nopcall/hitboard/HitboardAir/01_刷机/Pico正面.png

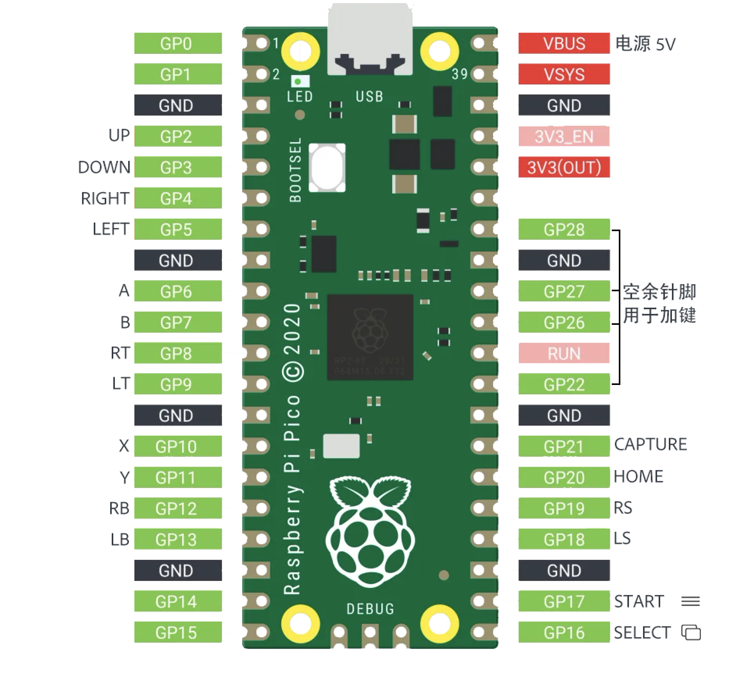
HitboardAir/01_刷机/Pico正面.png
