nopcall/hitboard/HitboardAir/02_3D_Files/images/00_按键.png

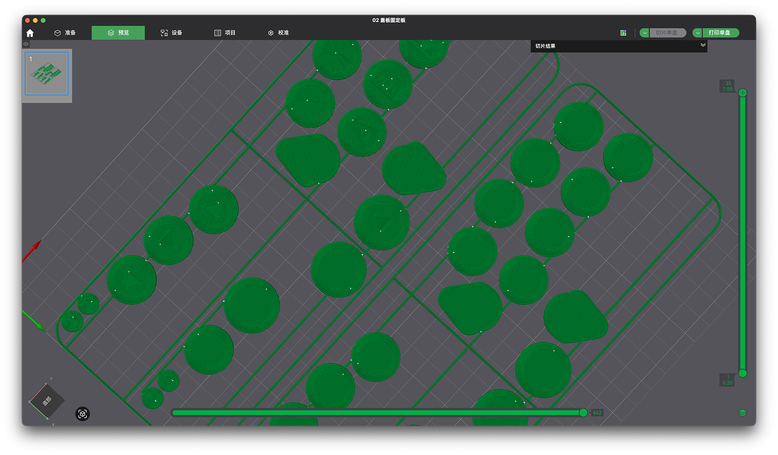
HitboardAir/02_3D_Files/images/00_按键.png
