nopcall/hitboard/HitboardAir/02_3D_Files/images/产品实拍_PLA.jpg

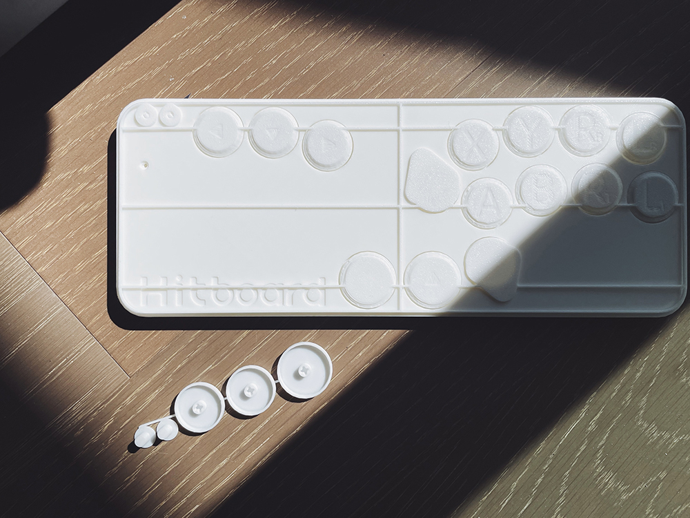
HitboardAir/02_3D_Files/images/产品实拍_PLA.jpg
