nopcall/hitboard/HitboardAir/02_3D_Files/More - 更多配件 /00_按键配件/配件_标准按键/00_圆润按键 （单个）/圆润按键.png

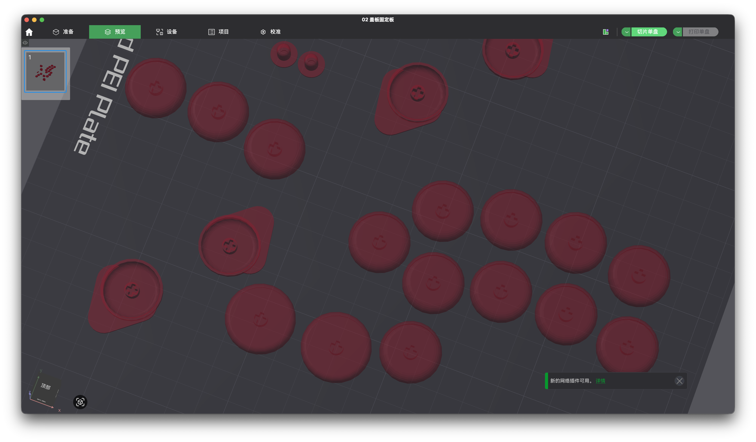
HitboardAir/02_3D_Files/More - 更多配件 /00_按键配件/配件_标准按键/00_圆润按键 （单个）/圆润按键.png
