nopcall/hitboard/HitboardAir/03_亚克力CAD文件/对称版/对称版布局示意图.png

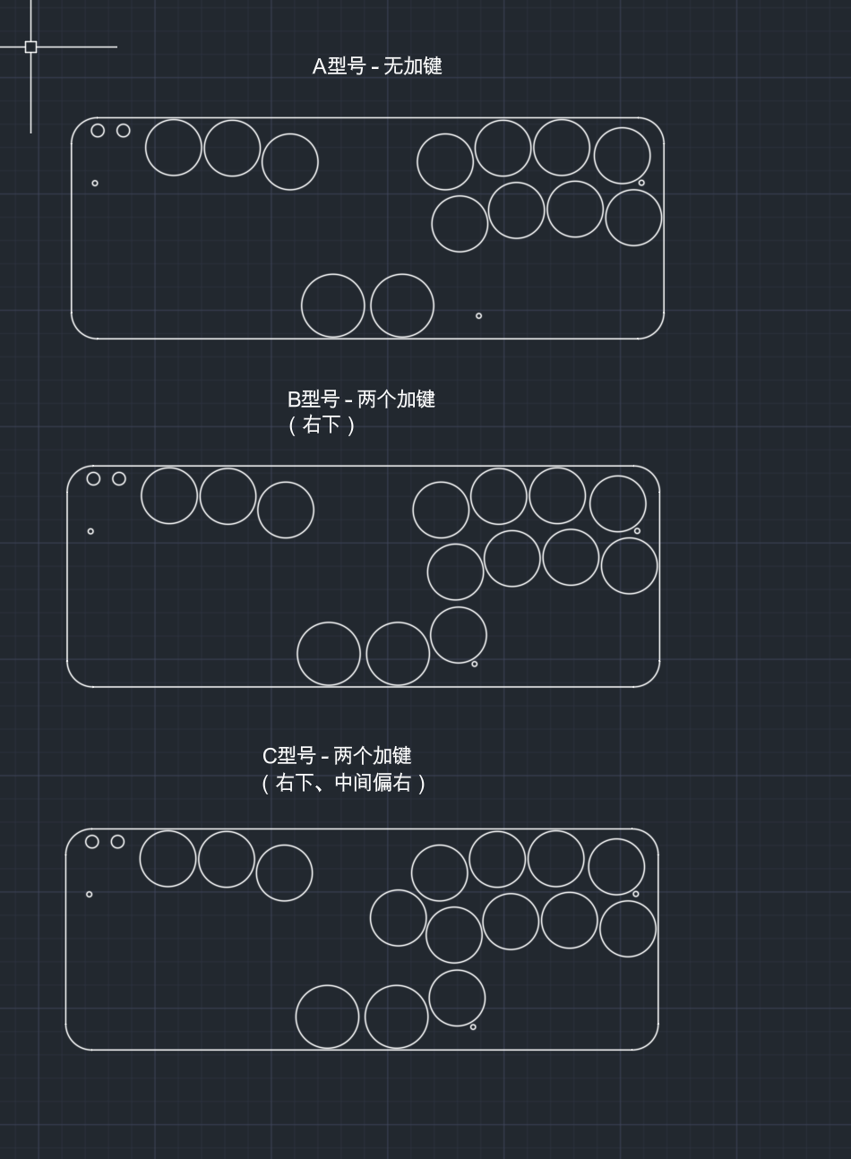
HitboardAir/03_亚克力CAD文件/对称版/对称版布局示意图.png
