nopcall/hitboard/HitboardAir/images/Dock.JPG

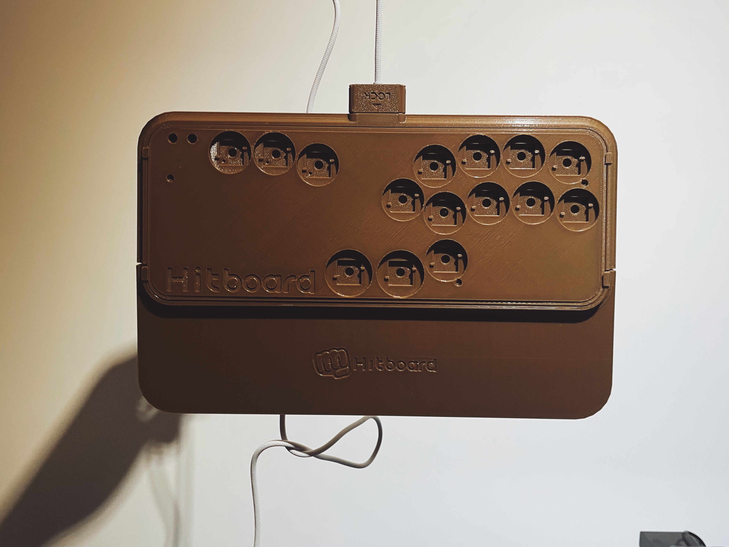
HitboardAir/images/Dock.JPG
