nopcall/hitboard/HitboardAir/images/FindYourFight03.png

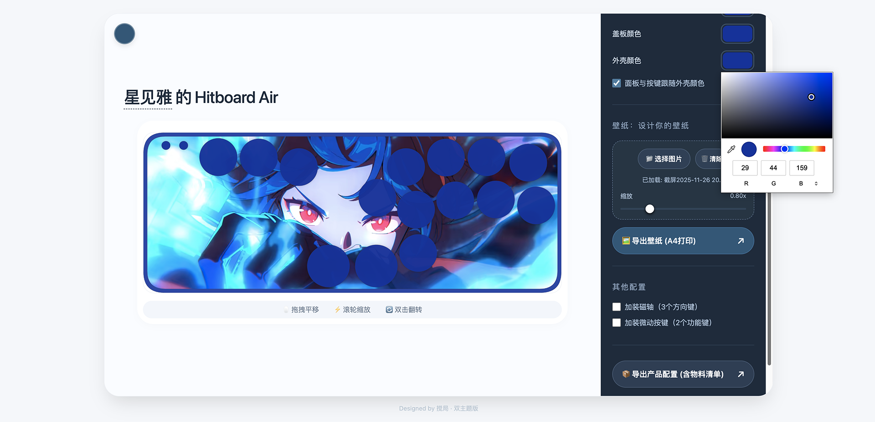
HitboardAir/images/FindYourFight03.png
