nopcall/hitboard/HitboardAir/images/FindYourFight04.png

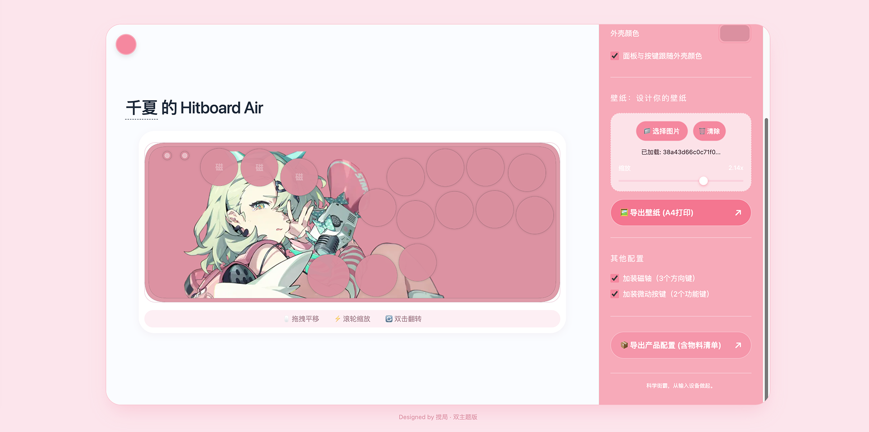
HitboardAir/images/FindYourFight04.png
