nopcall/hitboard/HitboardAir/images/边缘对比.JPG

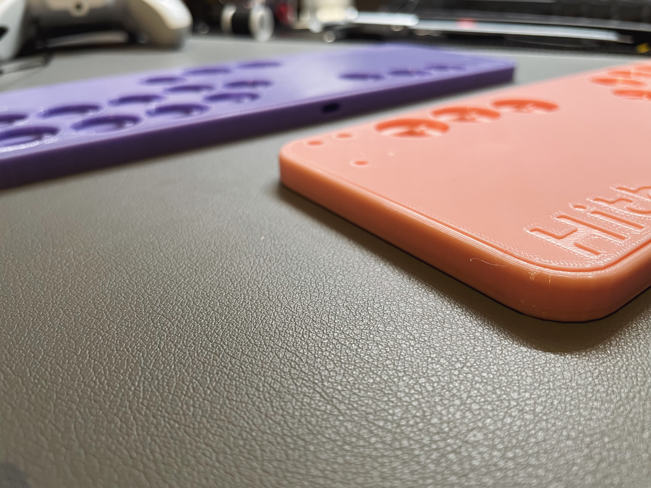
HitboardAir/images/边缘对比.JPG
