nopcall/hitboard/HitboardAir/其他/PCB 电路板/功能键电路板/PCB 小板.png

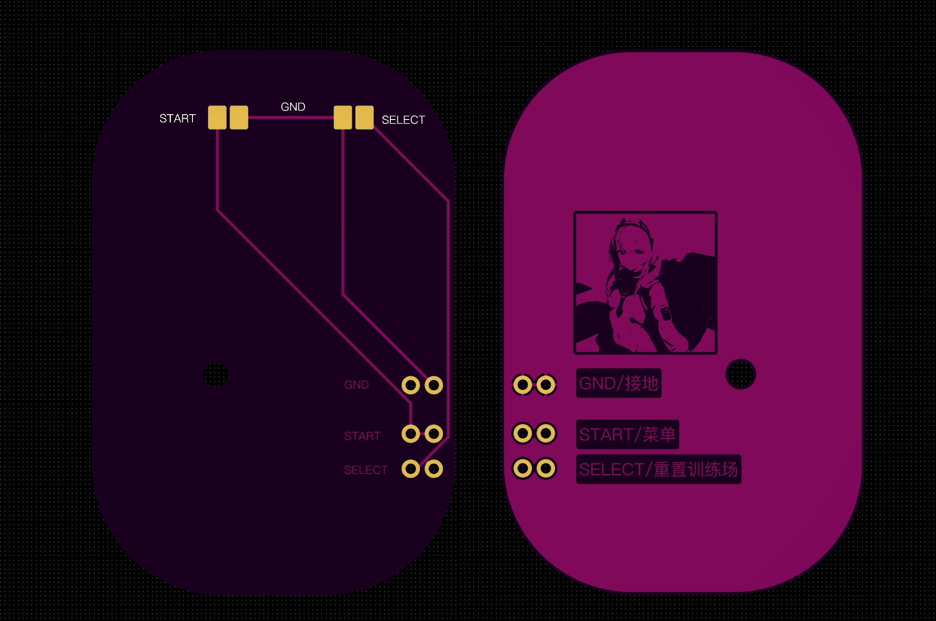
HitboardAir/其他/PCB 电路板/功能键电路板/PCB 小板.png
