nopcall/hitboard/HitboardClassic/02_3D_Files/Hitboard Classic/1-选择盖板/风格_街机:Hitbox/说明：盖板上下藏了 4 颗隐藏螺丝，如果有进一步固定需求，拿刀划开就行了.png

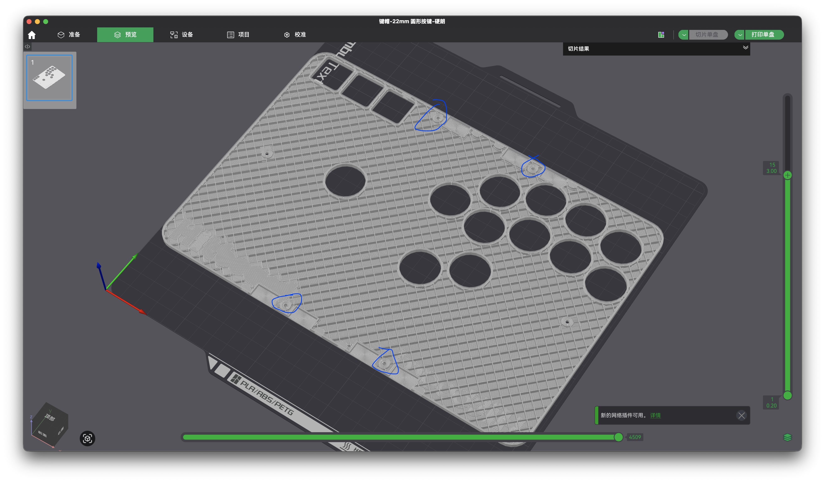
HitboardClassic/02_3D_Files/Hitboard Classic/1-选择盖板/风格_街机:Hitbox/说明：盖板上下藏了 4 颗隐藏螺丝，如果有进一步固定需求，拿刀划开就行了.png
