nopcall/hitboard/HitboardZero/元器件规格书/led 规格.png

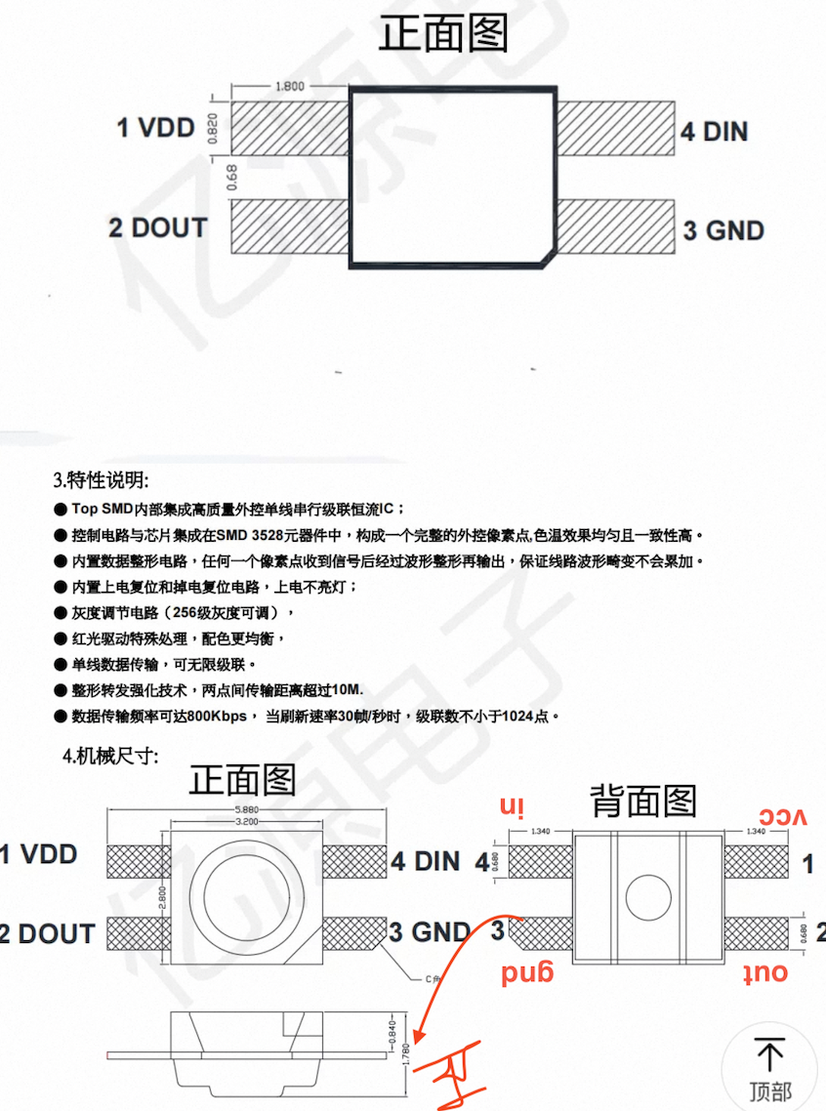
HitboardZero/元器件规格书/led 规格.png
