nopcall/hitboard/HitboardZero/元器件规格书/轴座规格.JPG

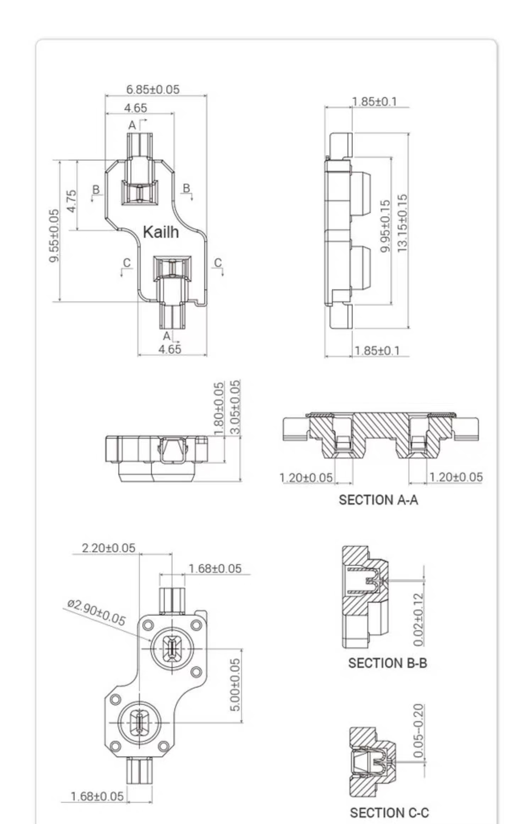
HitboardZero/元器件规格书/轴座规格.JPG
