nopcall/hitboard/HitboardClassic/02_3D_Files/Hitboard Classic - 大杯 L/新大杯 （L）/外壳-左半.stl

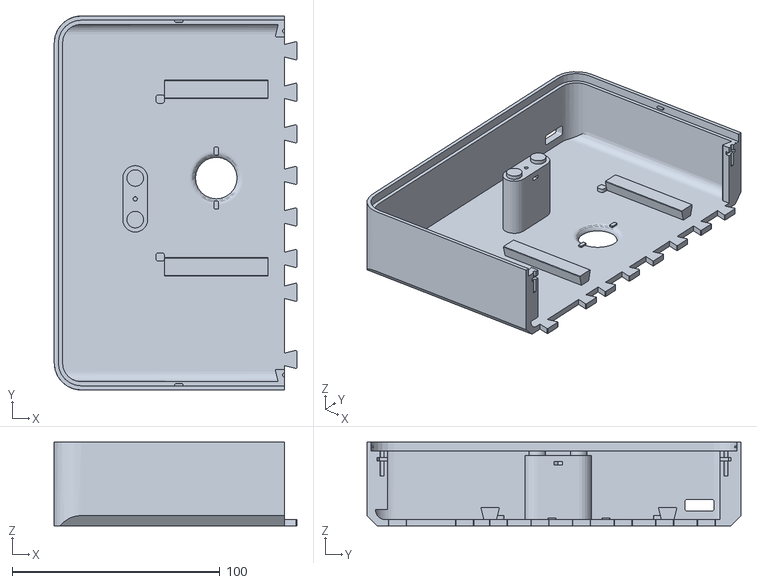
[picture p57: CAD file, 2026-05-05]
HitboardClassic/02_3D_Files/Hitboard Classic - 大杯 L/新大杯 （L）/外壳-左半.stl
116.7 x 180.0 x 40.4
