nopcall/hitboard/HitboardClassic/02_3D_Files/Hitboard Classic - 大杯 L/新大杯 （L）/更多（有完整外壳）/外壳-290x180.stl

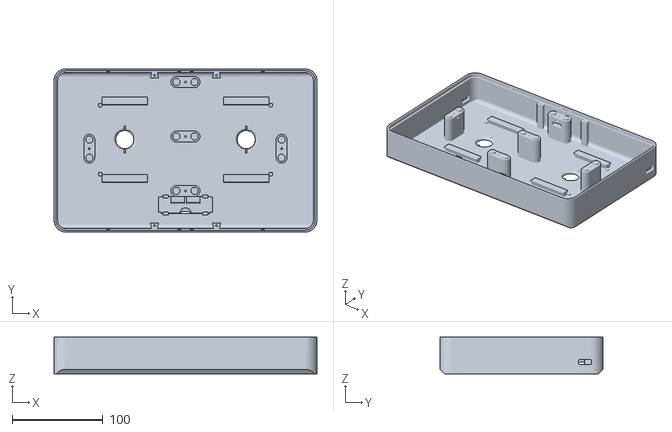
[picture p58: CAD file, 2026-05-06]
HitboardClassic/02_3D_Files/Hitboard Classic - 大杯 L/新大杯 （L）/更多（有完整外壳）/外壳-290x180.stl
290.0 x 180.0 x 40.4
