nopcall/hitboard/HitboardClassic/02_3D_Files/Hitboard Classic/1-选择盖板/风格_Mixbox/盖板-Mixbox（混合）.stl

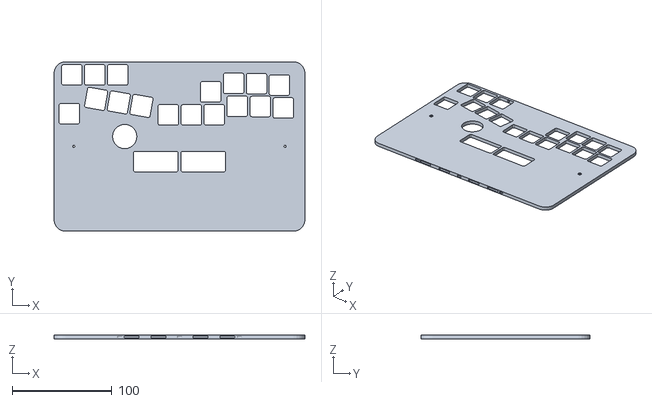
[picture p60: CAD file, 2026-05-03]
HitboardClassic/02_3D_Files/Hitboard Classic/1-选择盖板/风格_Mixbox/盖板-Mixbox（混合）.stl
252.0 x 170.0 x 4.00
