nopcall/hitboard/HitboardClassic/02_3D_Files/Hitboard Classic/1-选择盖板/风格_街机:Hitbox/盖板-街机（纯血）.stl

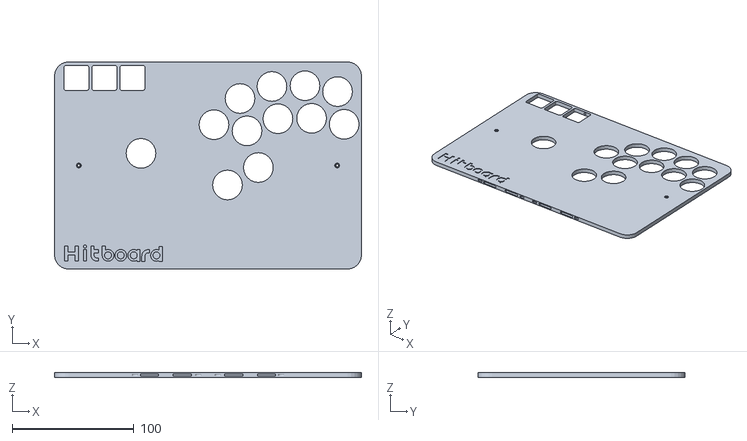
[picture p61: CAD file, 2026-05-04]
HitboardClassic/02_3D_Files/Hitboard Classic/1-选择盖板/风格_街机:Hitbox/盖板-街机（纯血）.stl
252.0 x 170.0 x 4.00
