nopcall/hitboard/HitboardClassic/02_3D_Files/Hitboard Classic/2-选择按键/街机:Hitbox/选项 B-凯华矮轴按键方案/键帽-22mm 圆形按键-圆润.stl

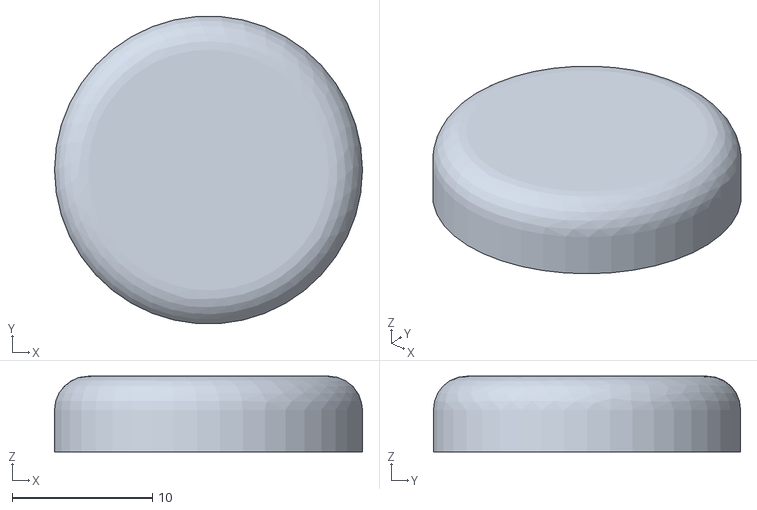
[picture p62: CAD file, 2026-05-10]
HitboardClassic/02_3D_Files/Hitboard Classic/2-选择按键/街机:Hitbox/选项 B-凯华矮轴按键方案/键帽-22mm 圆形按键-圆润.stl
22.0 x 21.9 x 5.40
