nopcall/hitboard/HitboardClassic/02_3D_Files/Hitboard Classic/3-选择外壳/外壳本体.stl

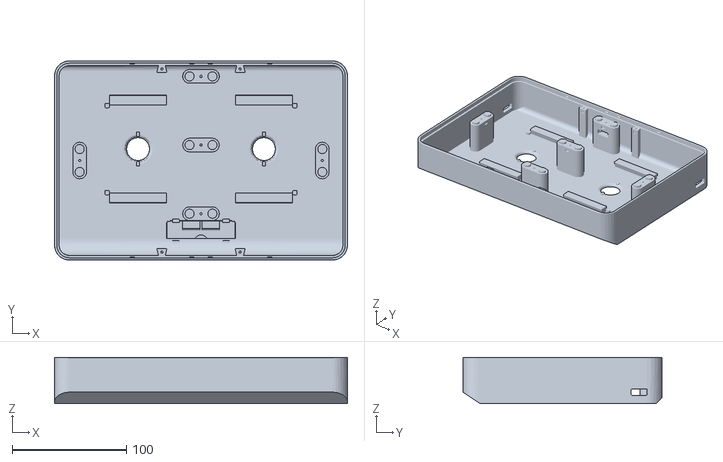
[picture p64: CAD file, 2026-05-05]
HitboardClassic/02_3D_Files/Hitboard Classic/3-选择外壳/外壳本体.stl
256.0 x 174.0 x 40.4
