nopcall/hitboard/HitboardClassic/02_3D_Files/Hitboard Classic/4-摇杆配件/摇杆色彩环.stl

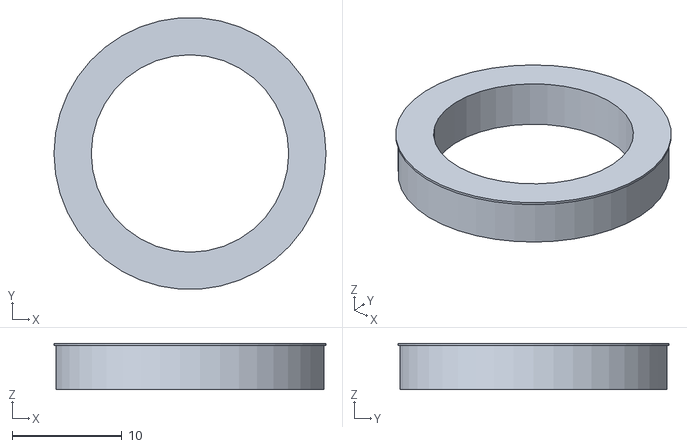
[picture p65: CAD file, 2026-04-30]
HitboardClassic/02_3D_Files/Hitboard Classic/4-摇杆配件/摇杆色彩环.stl
24.8 x 24.7 x 4.20
