nopcall/hitboard/HitboardClassic/02_3D_Files/More - 更多配件 /00_按键/01_轴座/轴座-Mixboard 宽按键-MX轴(打印时开启支撑).stl

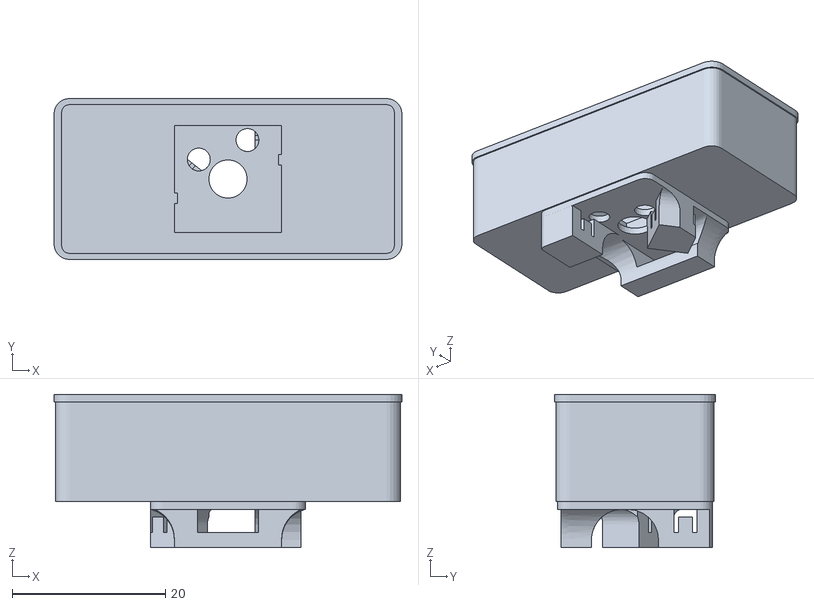
[picture p66: CAD file, 2026-05-03]
HitboardClassic/02_3D_Files/More - 更多配件 /00_按键/01_轴座/轴座-Mixboard 宽按键-MX轴(打印时开启支撑).stl
45.4 x 21.0 x 20.0
