nopcall/hitboard/HitboardClassic/02_3D_Files/More - 更多配件 /00_按键/02_矮轴按键/轴座-圆形按键-矮轴.stl

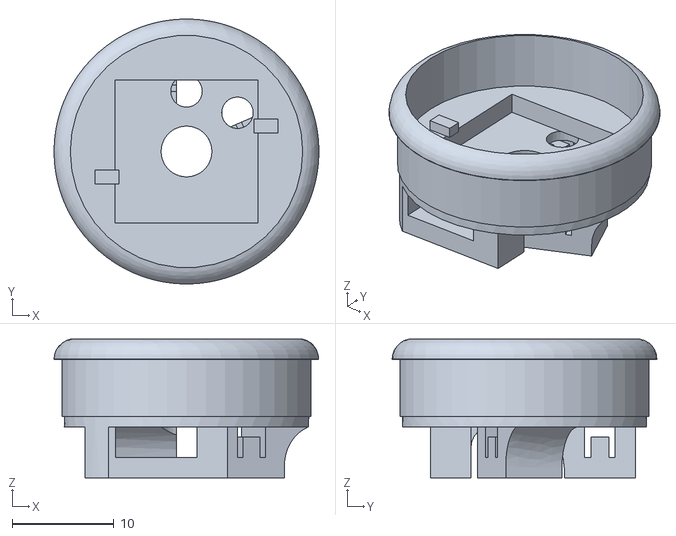
[picture p67: CAD file, 2026-04-30]
HitboardClassic/02_3D_Files/More - 更多配件 /00_按键/02_矮轴按键/轴座-圆形按键-矮轴.stl
26.0 x 26.0 x 13.6
