nopcall/hitboard/HitboardClassic/02_3D_Files/More - 更多配件 /01_盖板配件/封帽圆.stl

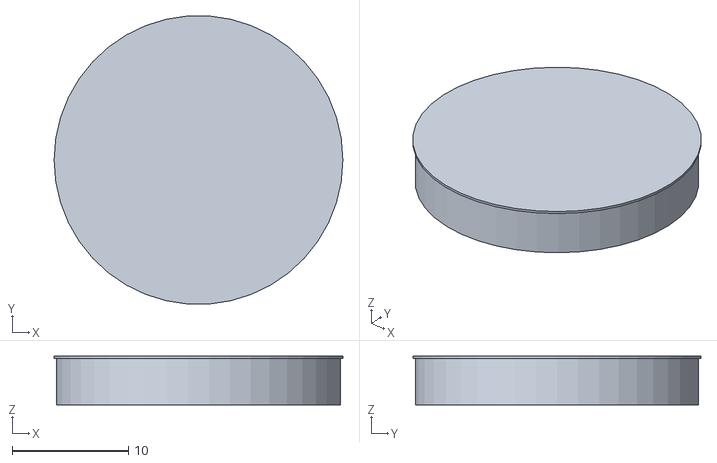
[picture p69: CAD file, 2026-04-30]
HitboardClassic/02_3D_Files/More - 更多配件 /01_盖板配件/封帽圆.stl
24.8 x 24.7 x 4.20
