nopcall/hitboard/HitboardClassic/02_3D_Files/More - 更多配件 /02_外壳配件/封帽-typec接口.stl

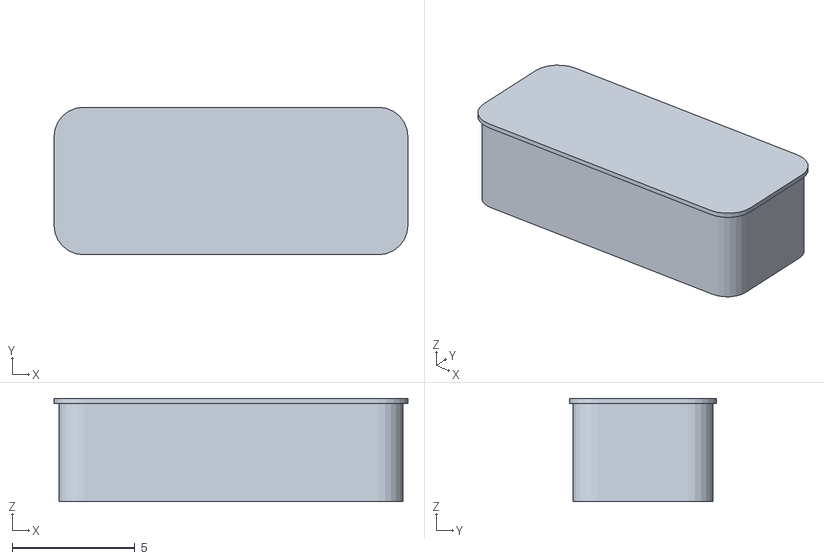
[picture p70: CAD file, 2026-05-03]
HitboardClassic/02_3D_Files/More - 更多配件 /02_外壳配件/封帽-typec接口.stl
14.4 x 6.00 x 4.20
