nopcall/hitboard/HitboardClassic/02_3D_Files/More - 更多配件 /03_其他配件/壁纸支撑板/支撑板-标准版-Mixbox.stl

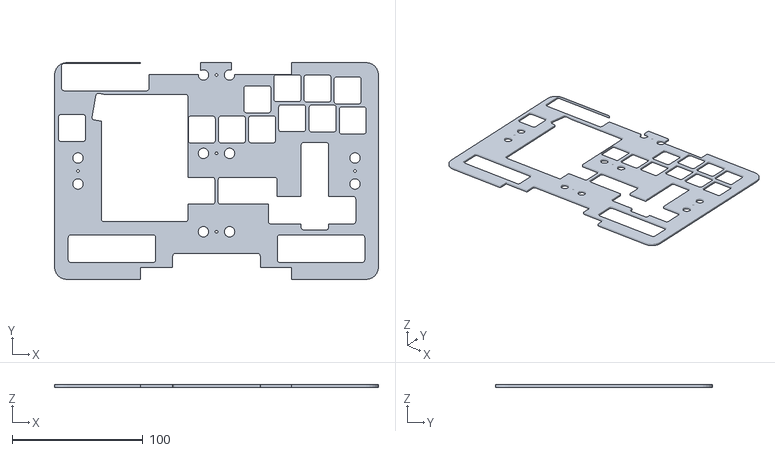
[picture p71: CAD file, 2026-04-28]
HitboardClassic/02_3D_Files/More - 更多配件 /03_其他配件/壁纸支撑板/支撑板-标准版-Mixbox.stl
248.0 x 166.0 x 2.00
