nopcall/hitboard/HitboardClassic/02_3D_Files/More - 更多配件 /03_其他配件/电源套件/电池仓 2 节 5 号.stl

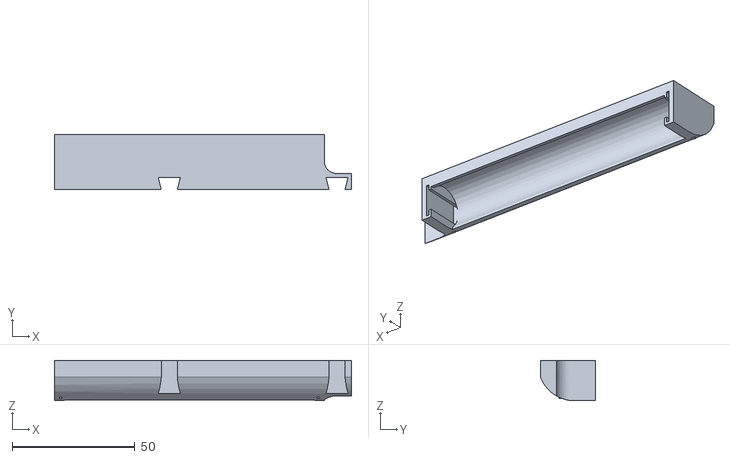
[picture p72: CAD file, 2026-05-03]
HitboardClassic/02_3D_Files/More - 更多配件 /03_其他配件/电源套件/电池仓 2 节 5 号.stl
121.1 x 22.6 x 16.5
