nopcall/hitboard/HitboardClassic/02_3D_Files/More - 更多配件 /03_其他配件/试轴器-圆 x3.stl

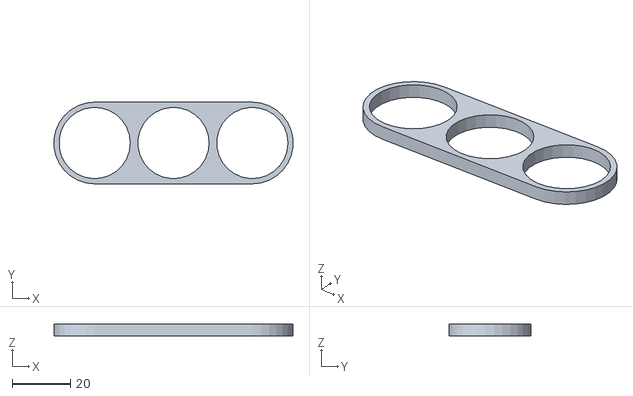
[picture p73: CAD file, 2026-04-30]
HitboardClassic/02_3D_Files/More - 更多配件 /03_其他配件/试轴器-圆 x3.stl
81.8 x 28.0 x 4.00
