nopcall/hitboard/HitboardAir/02_3D_Files/180x180 打印机（A1mini ）/七星版（可加 w、shift 键）/圆润/04_外壳_圆润_右半.stl

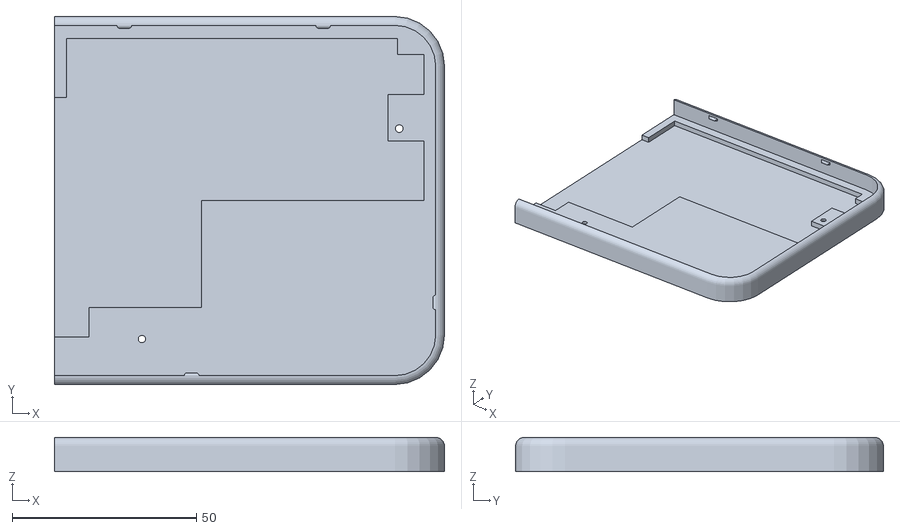
[picture p74: CAD file, 2026-04-25]
HitboardAir/02_3D_Files/180x180 打印机（A1mini ）/七星版（可加 w、shift 键）/圆润/04_外壳_圆润_右半.stl
106.0 x 100.0 x 9.30
