nopcall/hitboard/HitboardAir/02_3D_Files/180x180 打印机（A1mini ）/对称版/圆润/04_外壳_圆润_左半.stl

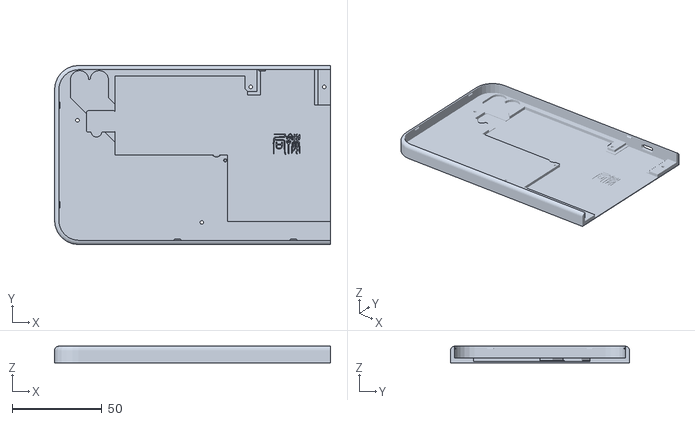
[picture p76: CAD file, 2026-04-25]
HitboardAir/02_3D_Files/180x180 打印机（A1mini ）/对称版/圆润/04_外壳_圆润_左半.stl
154.0 x 100.0 x 9.30
