nopcall/hitboard/HitboardAir/02_3D_Files/Hitboard Air - 七星版（拳皇:绝区零:音游）/圆润线条/03 线路板.stl

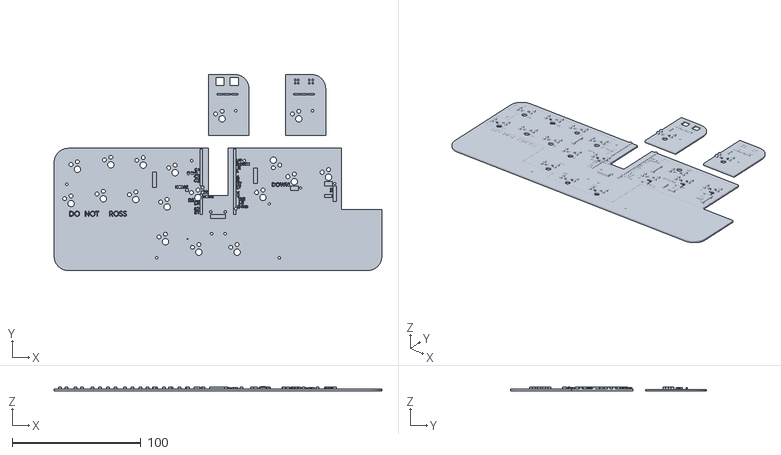
[picture p77: CAD file, 2026-04-25]
HitboardAir/02_3D_Files/Hitboard Air - 七星版（拳皇:绝区零:音游）/圆润线条/03 线路板.stl
255.2 x 152.6 x 3.50
