nopcall/hitboard/HitboardAir/02_3D_Files/More - 更多配件 /00_按键配件/配件_加键/圆形（22mm 直径）.stl

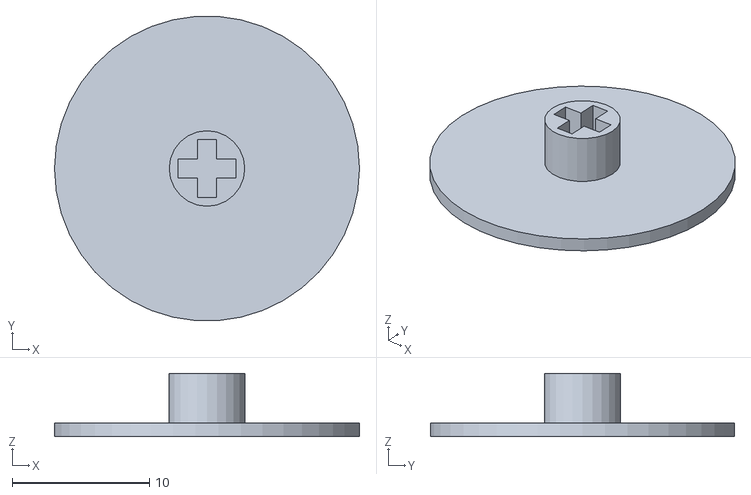
[picture p80: CAD file, 2026-04-25]
HitboardAir/02_3D_Files/More - 更多配件 /00_按键配件/配件_加键/圆形（22mm 直径）.stl
22.2 x 22.1 x 4.60
