nopcall/hitboard/HitboardAir/02_3D_Files/More - 更多配件 /02_盖板配件/23mm 按键封帽_改方孔.stl

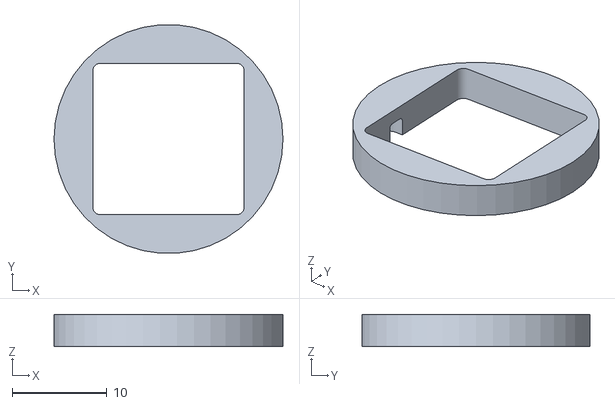
[picture p81: CAD file, 2026-04-25]
HitboardAir/02_3D_Files/More - 更多配件 /02_盖板配件/23mm 按键封帽_改方孔.stl
24.2 x 24.1 x 3.40
