nopcall/hitboard/HitboardAir/02_3D_Files/More - 更多配件 /03_线路板配件/03_小板_缠线适配导电胶.stl

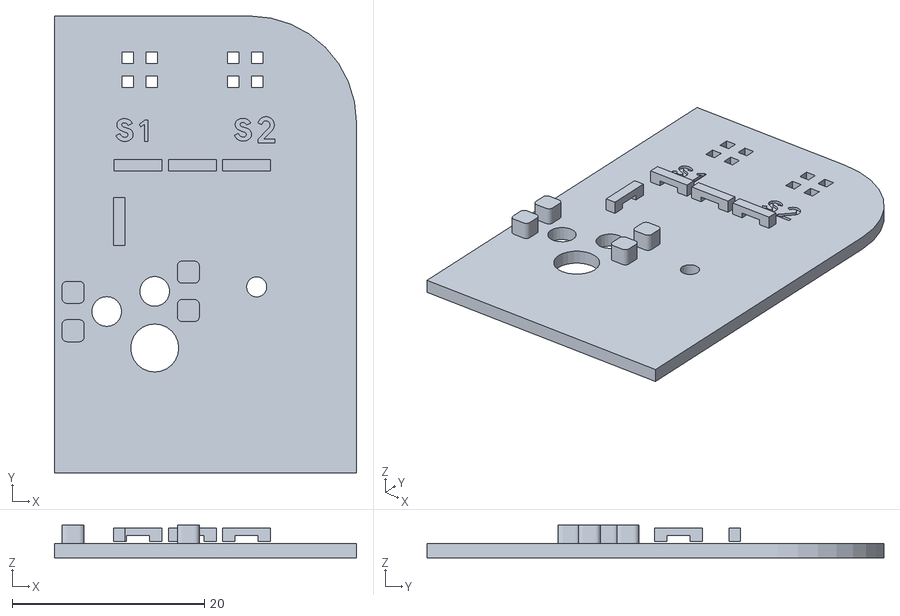
[picture p82: CAD file, 2026-04-25]
HitboardAir/02_3D_Files/More - 更多配件 /03_线路板配件/03_小板_缠线适配导电胶.stl
31.5 x 47.6 x 3.40
