nopcall/hitboard/HitboardClassic/02_3D_Files/Hitboard Classic - 大杯 L/新大杯 （L）/外壳-右半.stl

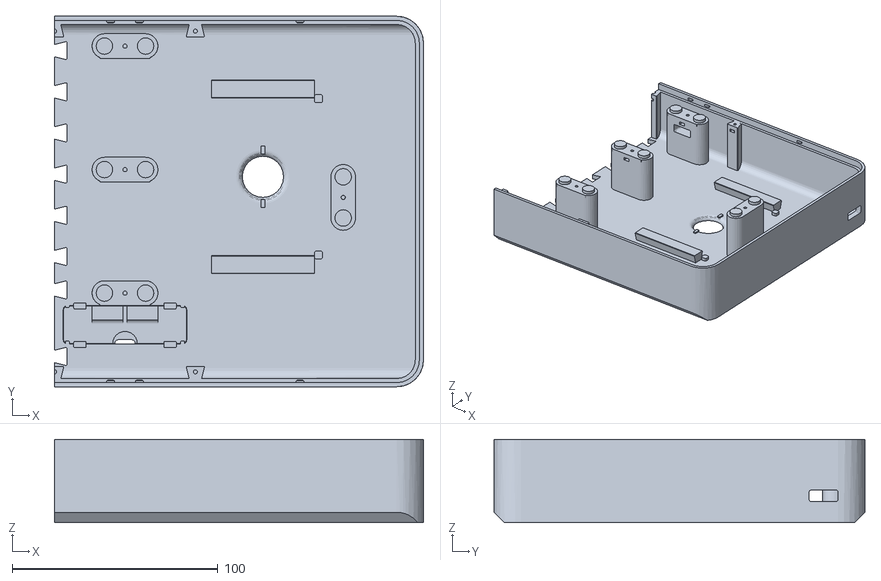
[picture p84: CAD file, 2026-05-05]
HitboardClassic/02_3D_Files/Hitboard Classic - 大杯 L/新大杯 （L）/外壳-右半.stl
179.2 x 180.0 x 40.4
