nopcall/hitboard/HitboardClassic/02_3D_Files/Hitboard Classic - 大杯 L/新大杯 （L）/更多（有完整外壳）/盖板-左半（带 Hitbox 方向键开孔）.stl

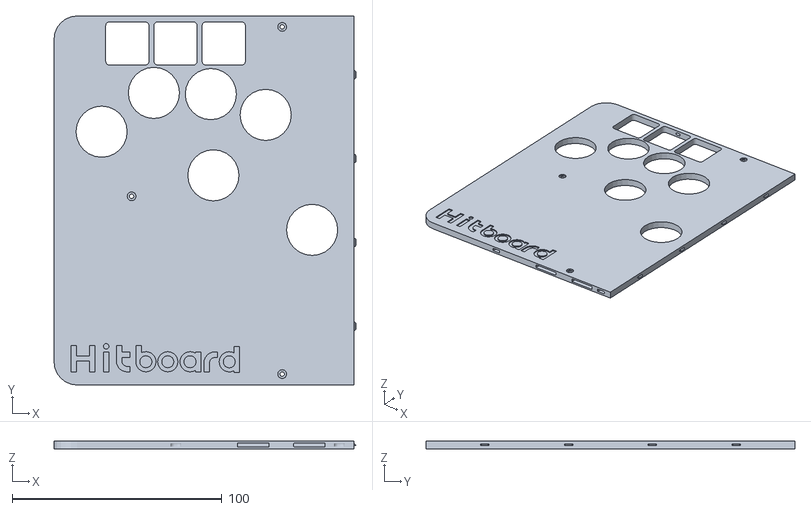
[picture p85: CAD file, 2026-05-04]
HitboardClassic/02_3D_Files/Hitboard Classic - 大杯 L/新大杯 （L）/更多（有完整外壳）/盖板-左半（带 Hitbox 方向键开孔）.stl
144.0 x 176.0 x 4.00
