nopcall/hitboard/HitboardClassic/02_3D_Files/Hitboard Classic/1-选择盖板/风格_Mixbox/180x180 打印机（A1mini ）/盖板-Mixbox（纯血）左.stl

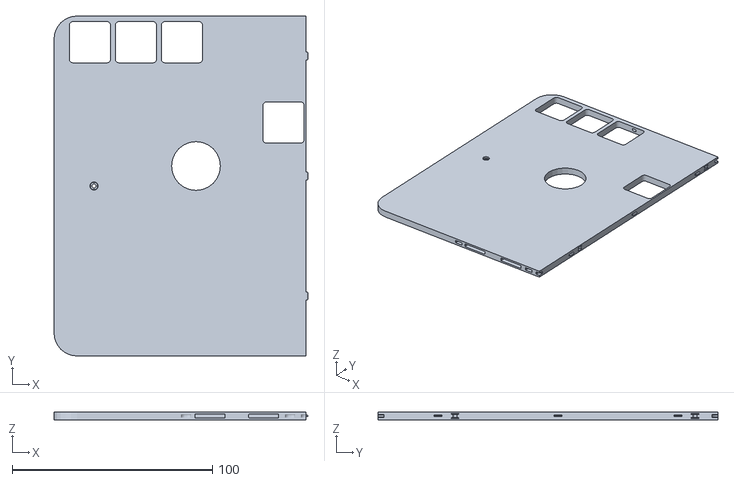
[picture p86: CAD file, 2026-05-03]
HitboardClassic/02_3D_Files/Hitboard Classic/1-选择盖板/风格_Mixbox/180x180 打印机（A1mini ）/盖板-Mixbox（纯血）左.stl
127.0 x 170.0 x 4.00
