nopcall/hitboard/HitboardClassic/02_3D_Files/Hitboard Classic/1-选择盖板/风格_街机:Hitbox/180x180 打印机（A1mini ）/盖板-街机（纯血）左.stl

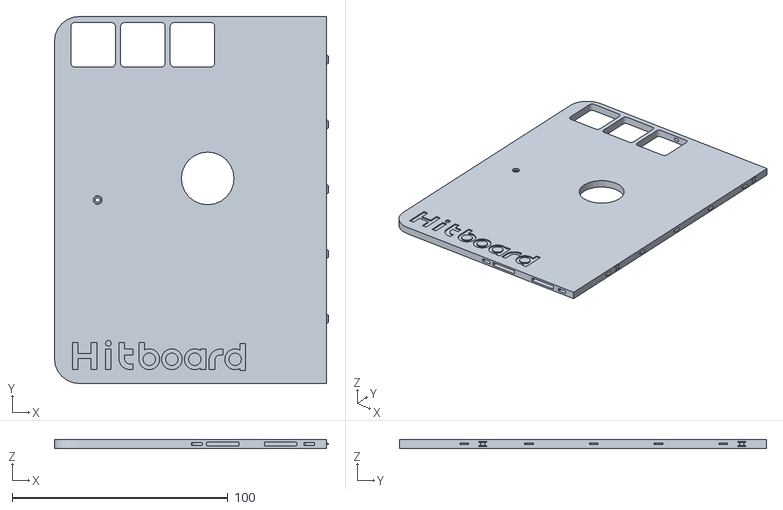
[picture p87: CAD file, 2026-05-04]
HitboardClassic/02_3D_Files/Hitboard Classic/1-选择盖板/风格_街机:Hitbox/180x180 打印机（A1mini ）/盖板-街机（纯血）左.stl
127.0 x 170.0 x 4.00
