nopcall/hitboard/HitboardClassic/02_3D_Files/Hitboard Classic/3-选择外壳/180x180 打印机（A1mini ）/外壳左半.stl

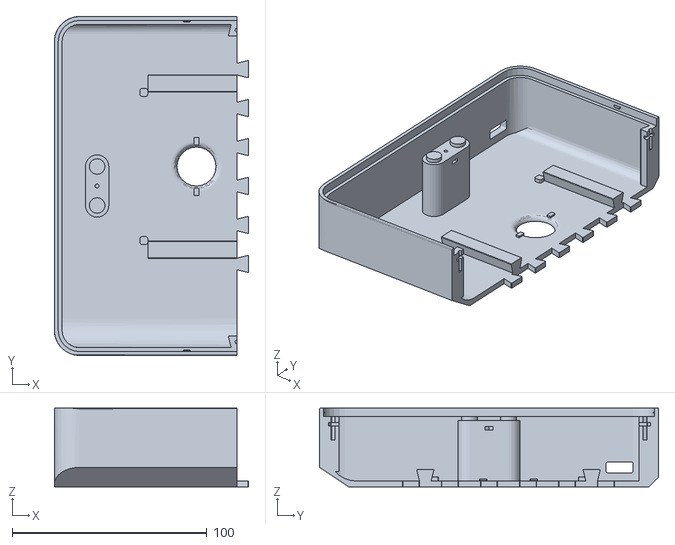
[picture p88: CAD file, 2026-05-05]
HitboardClassic/02_3D_Files/Hitboard Classic/3-选择外壳/180x180 打印机（A1mini ）/外壳左半.stl
99.8 x 174.0 x 40.4
