nopcall/hitboard/HitboardClassic/02_3D_Files/Hitboard Classic/3-选择外壳/外壳组件.stl

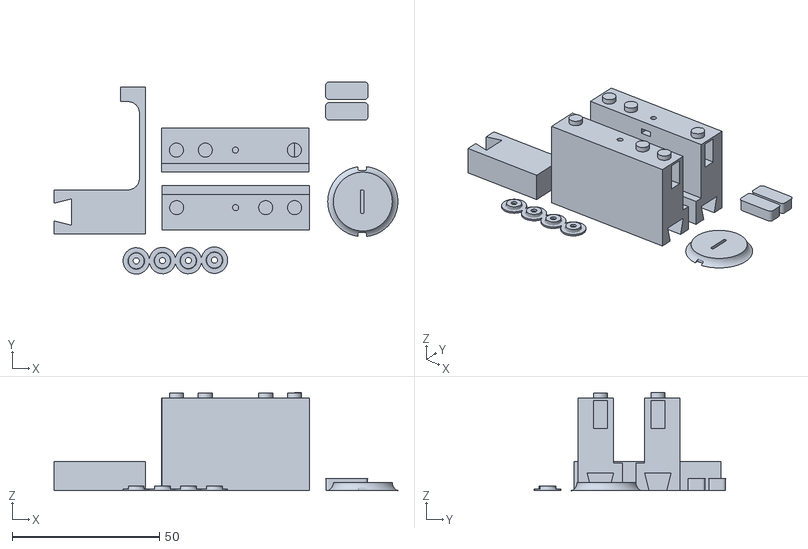
[picture p89: CAD file, 2026-05-04]
HitboardClassic/02_3D_Files/Hitboard Classic/3-选择外壳/外壳组件.stl
116.7 x 65.2 x 33.4
