nopcall/hitboard/HitboardClassic/02_3D_Files/Hitboard Classic/4-摇杆配件/摇杆防尘片.stl

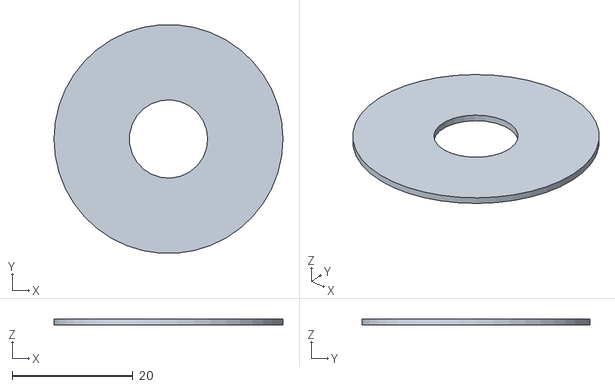
[picture p90: CAD file, 2026-04-22]
HitboardClassic/02_3D_Files/Hitboard Classic/4-摇杆配件/摇杆防尘片.stl
38.0 x 37.9 x 1
