nopcall/hitboard/HitboardClassic/02_3D_Files/More - 更多配件 /00_按键/01_轴座/轴座-功能键-矮轴.stl

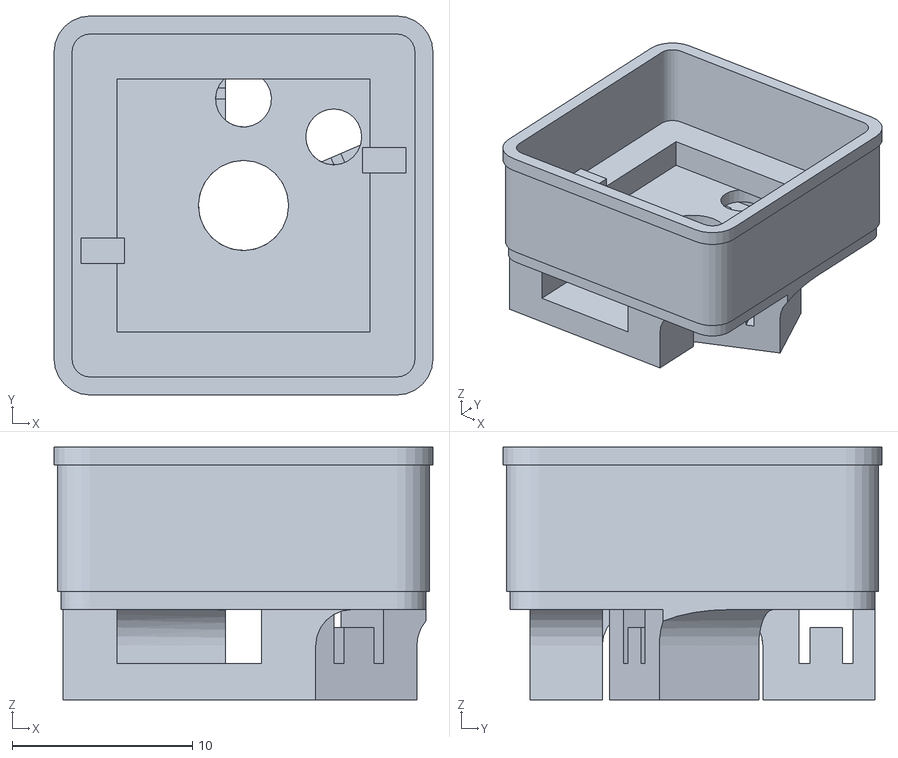
[picture p92: CAD file, 2026-05-03]
HitboardClassic/02_3D_Files/More - 更多配件 /00_按键/01_轴座/轴座-功能键-矮轴.stl
21.0 x 21.0 x 14.0
