nopcall/hitboard/HitboardClassic/02_3D_Files/More - 更多配件 /01_盖板配件/封帽-Shift.stl

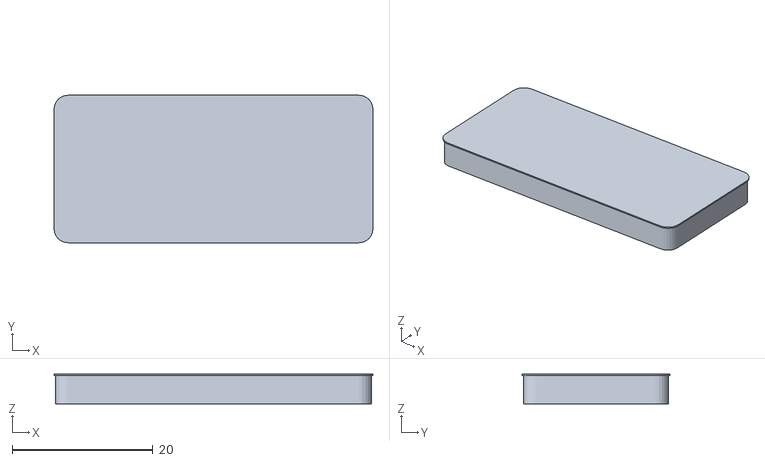
[picture p93: CAD file, 2026-04-27]
HitboardClassic/02_3D_Files/More - 更多配件 /01_盖板配件/封帽-Shift.stl
45.4 x 21.0 x 4.20
