nopcall/hitboard/HitboardClassic/02_3D_Files/More - 更多配件 /02_外壳配件/轨道-摇杆台（宝联:拳霸）.stl

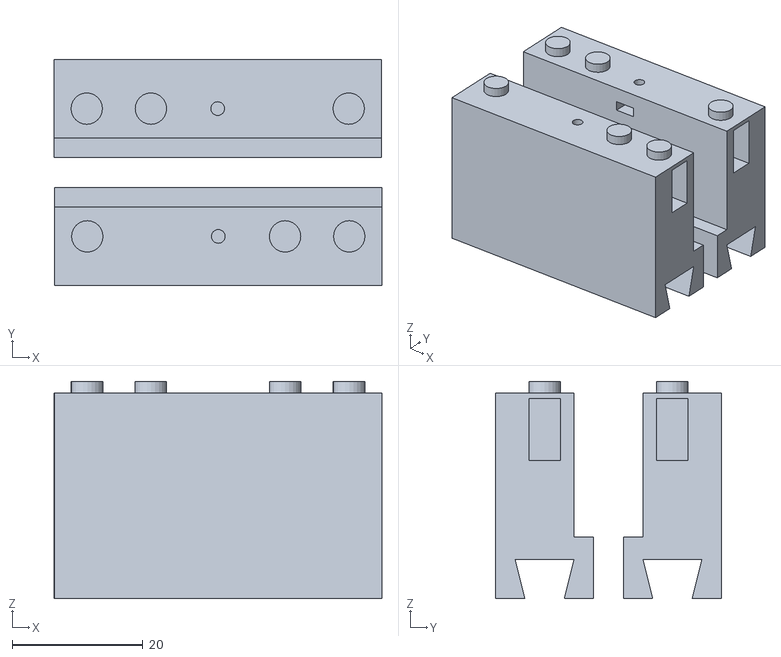
[picture p94: CAD file, 2026-05-03]
HitboardClassic/02_3D_Files/More - 更多配件 /02_外壳配件/轨道-摇杆台（宝联:拳霸）.stl
50.1 x 34.5 x 33.2
