nopcall/hitboard/HitboardClassic/02_3D_Files/More - 更多配件 /03_其他配件/电源套件/电池仓 3 节 5 号.stl

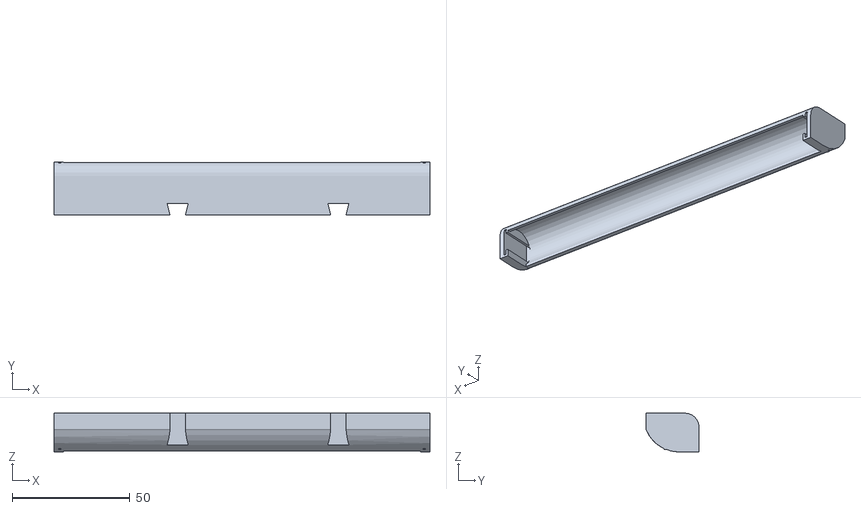
[picture p95: CAD file, 2026-05-03]
HitboardClassic/02_3D_Files/More - 更多配件 /03_其他配件/电源套件/电池仓 3 节 5 号.stl
160.0 x 22.6 x 16.5
