nopcall/hitboard/HitboardClassic/02_3D_Files/More - 更多配件 /03_其他配件/试轴器-方 x3.stl

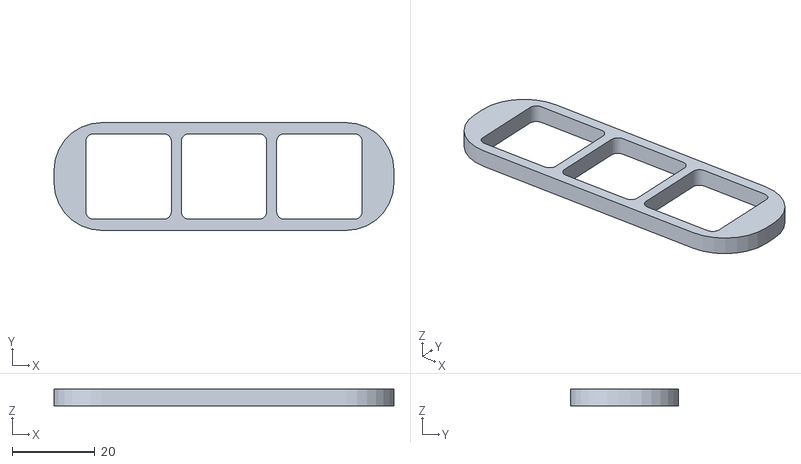
[picture p96: CAD file, 2026-04-27]
HitboardClassic/02_3D_Files/More - 更多配件 /03_其他配件/试轴器-方 x3.stl
82.0 x 26.0 x 4.00
