nopcall/hitboard/HitboardClassic/02_3D_Files/More - 更多配件 /内测入口/用于23mm 键帽（会不兼容 24mm 街机按键）/盖板（大杯右侧）（左侧不需要改）.stl

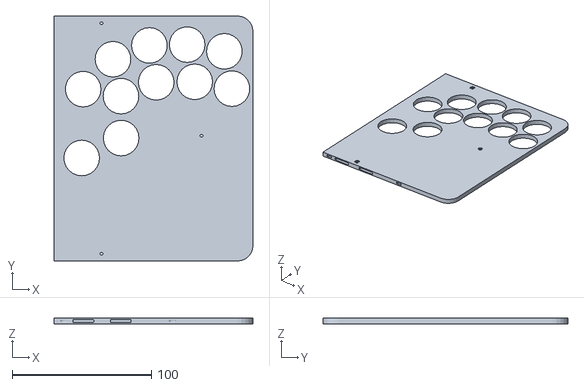
[picture p97: CAD file, 2026-05-09]
HitboardClassic/02_3D_Files/More - 更多配件 /内测入口/用于23mm 键帽（会不兼容 24mm 街机按键）/盖板（大杯右侧）（左侧不需要改）.stl
143.0 x 176.0 x 4.00
