nopcall/hitboard/HitboardAir/02_3D_Files/180x180 打印机（A1mini ）/七星版（可加 w、shift 键）/圆润/01_盖板_右半.stl

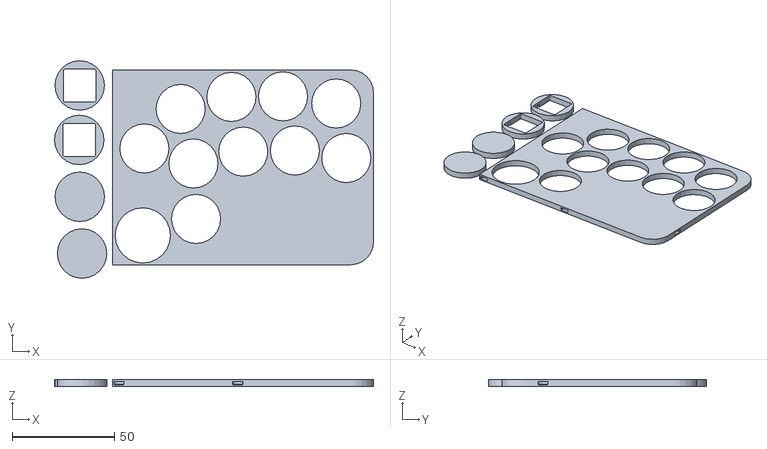
[picture p98: CAD file, 2026-04-25]
HitboardAir/02_3D_Files/180x180 打印机（A1mini ）/七星版（可加 w、shift 键）/圆润/01_盖板_右半.stl
155.9 x 106.3 x 3.40
