nopcall/hitboard/HitboardAir/02_3D_Files/More - 更多配件 /00_按键配件/配件_加键/三角形.stl

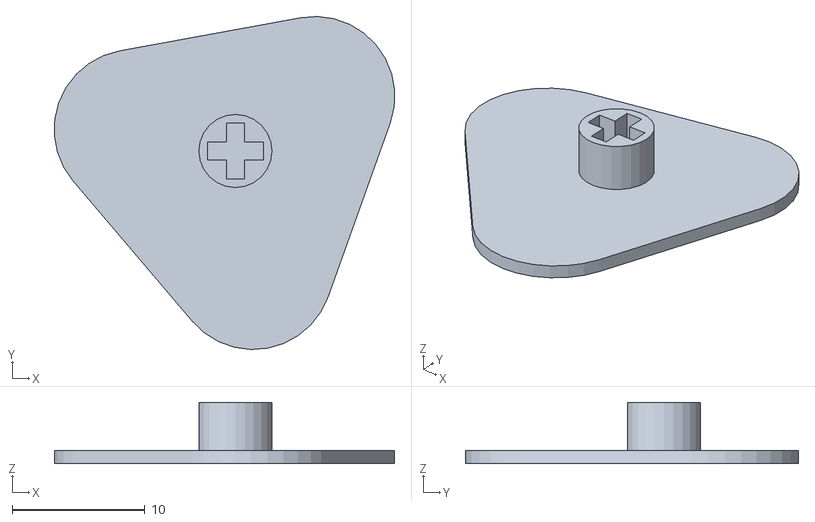
[picture p101: CAD file, 2026-04-25]
HitboardAir/02_3D_Files/More - 更多配件 /00_按键配件/配件_加键/三角形.stl
25.6 x 25.0 x 4.60
