nopcall/hitboard/HitboardAir/02_3D_Files/More - 更多配件 /02_盖板配件/w&shfit 封帽.stl

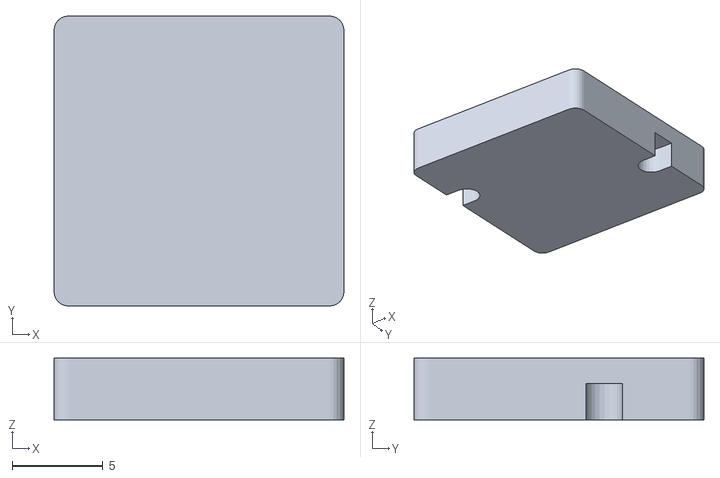
[picture p102: CAD file, 2026-04-25]
HitboardAir/02_3D_Files/More - 更多配件 /02_盖板配件/w&shfit 封帽.stl
16.0 x 16.0 x 3.40
