nopcall/hitboard/HitboardClassic/02_3D_Files/Hitboard Classic - 大杯 L/新大杯 （L）/更多（有完整外壳）/盖板-290x180.stl

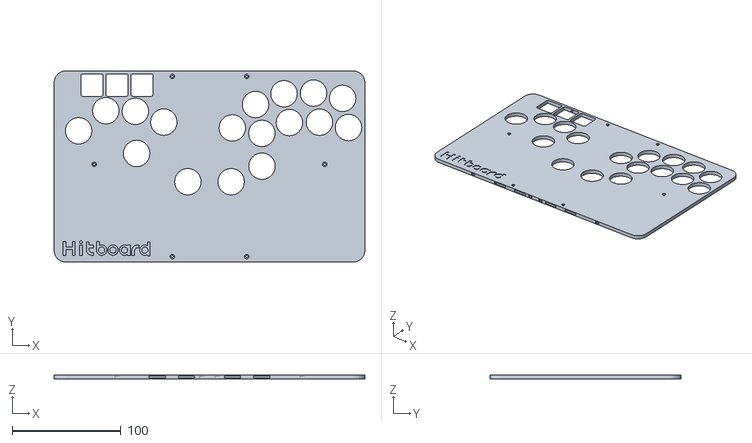
[picture p104: CAD file, 2026-05-04]
HitboardClassic/02_3D_Files/Hitboard Classic - 大杯 L/新大杯 （L）/更多（有完整外壳）/盖板-290x180.stl
286.0 x 176.0 x 4.00
