nopcall/hitboard/HitboardClassic/02_3D_Files/Hitboard Classic - 大杯 L/新大杯 （L）/盖板-右半.stl

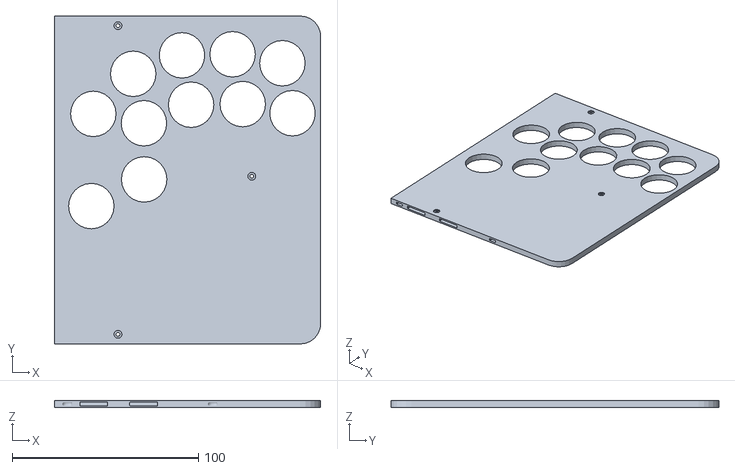
[picture p105: CAD file, 2026-05-04]
HitboardClassic/02_3D_Files/Hitboard Classic - 大杯 L/新大杯 （L）/盖板-右半.stl
143.0 x 176.0 x 4.00
