nopcall/hitboard/HitboardClassic/02_3D_Files/Hitboard Classic/3-选择外壳/180x180 打印机（A1mini ）/外壳锁扣（打印两个）.stl

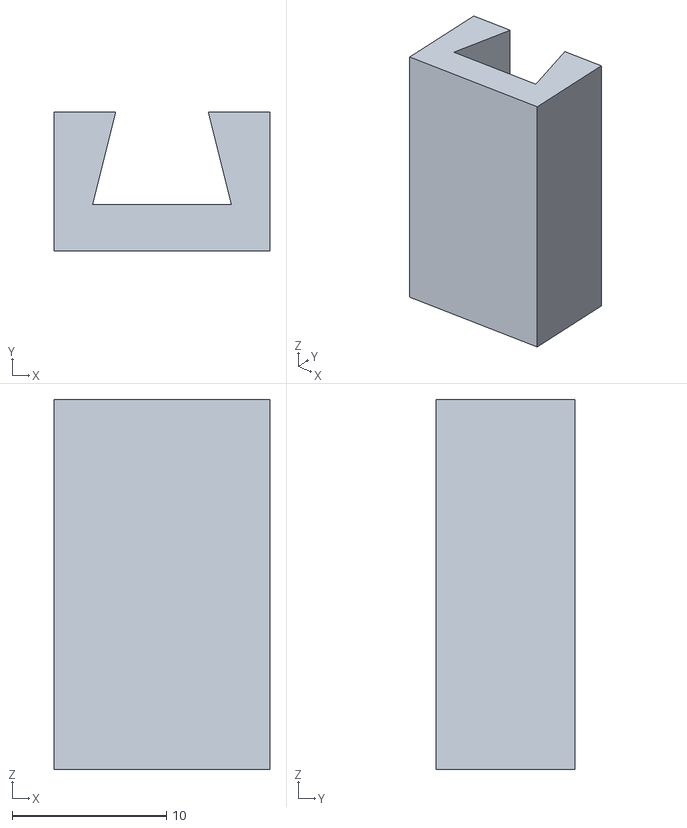
[picture p106: CAD file, 2026-04-23]
HitboardClassic/02_3D_Files/Hitboard Classic/3-选择外壳/180x180 打印机（A1mini ）/外壳锁扣（打印两个）.stl
14.0 x 9.00 x 24.0
