nopcall/hitboard/HitboardClassic/02_3D_Files/Hitboard Classic/4-摇杆配件/摇杆限位环-圆方.stl

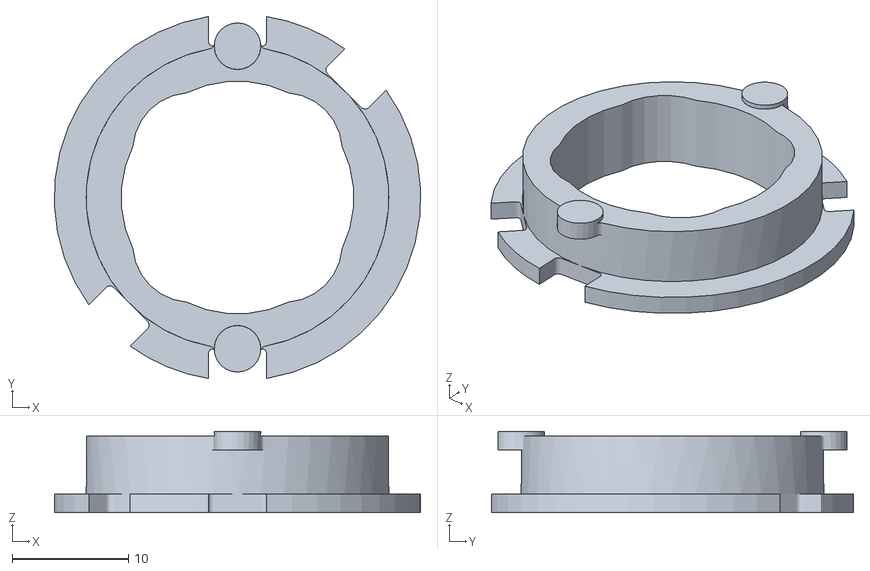
[picture p107: CAD file, 2026-04-22]
HitboardClassic/02_3D_Files/Hitboard Classic/4-摇杆配件/摇杆限位环-圆方.stl
31.5 x 31.1 x 7.00
