nopcall/hitboard/HitboardClassic/02_3D_Files/More - 更多配件 /00_按键/00_键帽/键帽-功能键-三和轴.stl

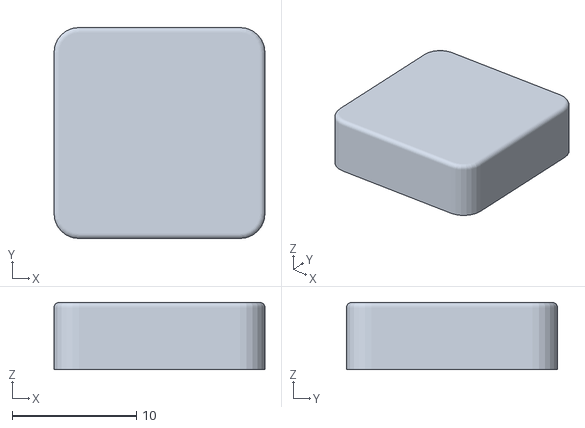
[picture p108: CAD file, 2026-04-30]
HitboardClassic/02_3D_Files/More - 更多配件 /00_按键/00_键帽/键帽-功能键-三和轴.stl
17.0 x 17.0 x 5.40
