nopcall/hitboard/HitboardClassic/02_3D_Files/More - 更多配件 /01_盖板配件/封帽-方.stl

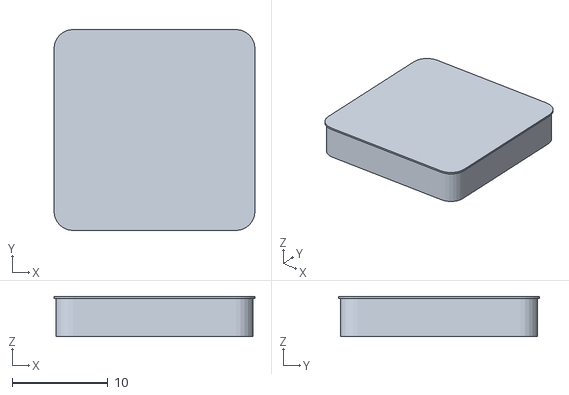
[picture p110: CAD file, 2026-04-27]
HitboardClassic/02_3D_Files/More - 更多配件 /01_盖板配件/封帽-方.stl
21.0 x 21.0 x 4.20
