nopcall/hitboard/HitboardClassic/02_3D_Files/More - 更多配件 /03_其他配件/电源套件/电池盖.stl

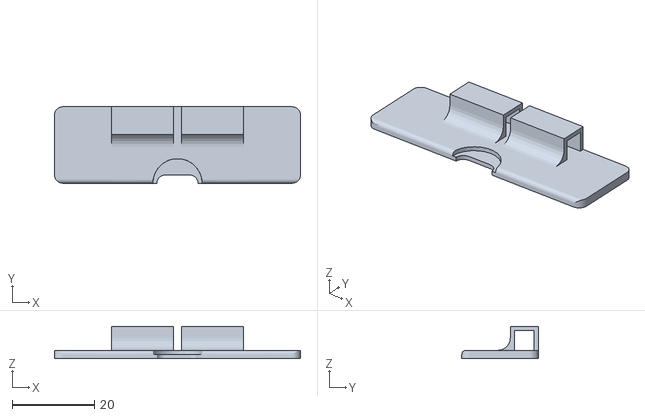
[picture p111: CAD file, 2026-05-03]
HitboardClassic/02_3D_Files/More - 更多配件 /03_其他配件/电源套件/电池盖.stl
59.8 x 18.6 x 7.80
