nopcall/hitboard/HitboardClassic/02_3D_Files/More - 更多配件 /内测入口/用于23mm 键帽（会不兼容 24mm 街机按键）/MX 轴.stl

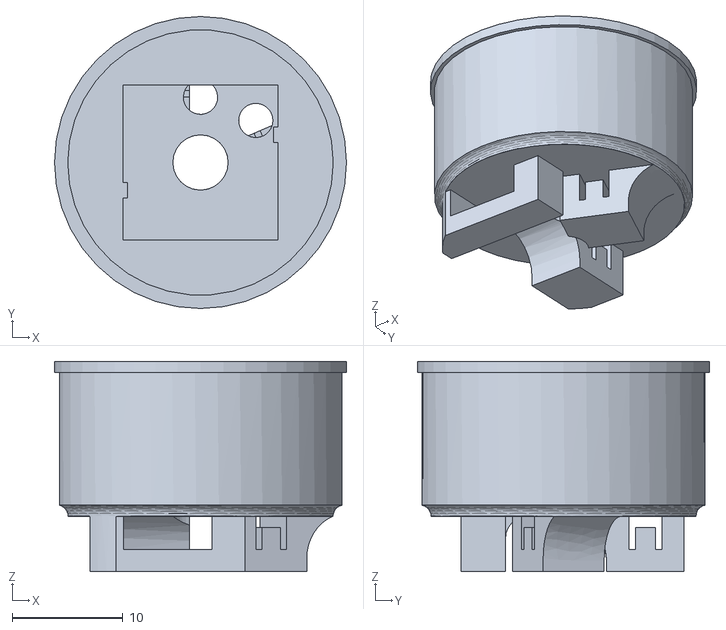
[picture p112: CAD file, 2026-05-09]
HitboardClassic/02_3D_Files/More - 更多配件 /内测入口/用于23mm 键帽（会不兼容 24mm 街机按键）/MX 轴.stl
26.4 x 26.4 x 19.0
