nopcall/hitboard/HitboardAir/02_3D_Files/More - 更多配件 /02_盖板配件/26mm 按键封帽_改方孔.stl

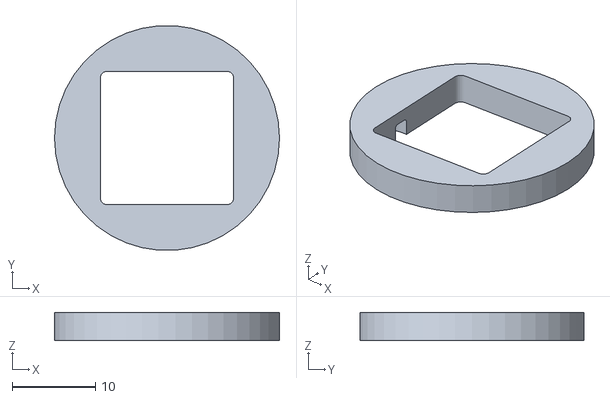
[picture p115: CAD file, 2026-04-25]
HitboardAir/02_3D_Files/More - 更多配件 /02_盖板配件/26mm 按键封帽_改方孔.stl
27.0 x 26.9 x 3.40
