nopcall/hitboard/HitboardClassic/02_3D_Files/Hitboard Classic - 大杯 L/新大杯 （L）/更多（有完整外壳）/外壳锁扣（打印两个）.stl

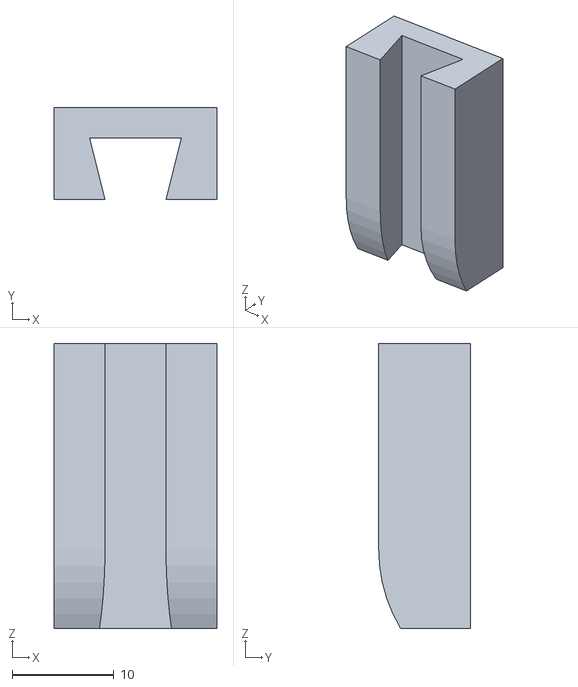
[picture p116: CAD file, 2026-04-29]
HitboardClassic/02_3D_Files/Hitboard Classic - 大杯 L/新大杯 （L）/更多（有完整外壳）/外壳锁扣（打印两个）.stl
16.0 x 9.00 x 28.0
