nopcall/hitboard/HitboardClassic/02_3D_Files/More - 更多配件 /02_外壳配件/封帽-底洞.stl

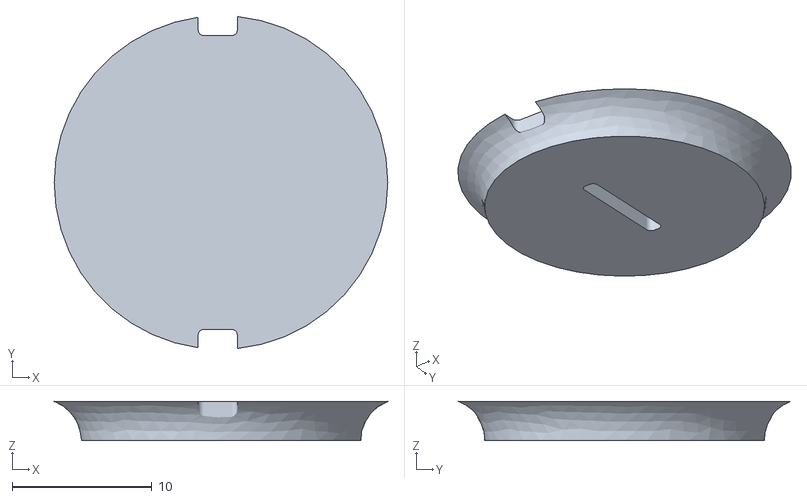
[picture p120: CAD file, 2026-04-23]
HitboardClassic/02_3D_Files/More - 更多配件 /02_外壳配件/封帽-底洞.stl
23.8 x 23.7 x 2.80
