nopcall/hitboard/HitboardClassic/02_3D_Files/More - 更多配件 /03_其他配件/电源套件/拨杆开关底座.stl

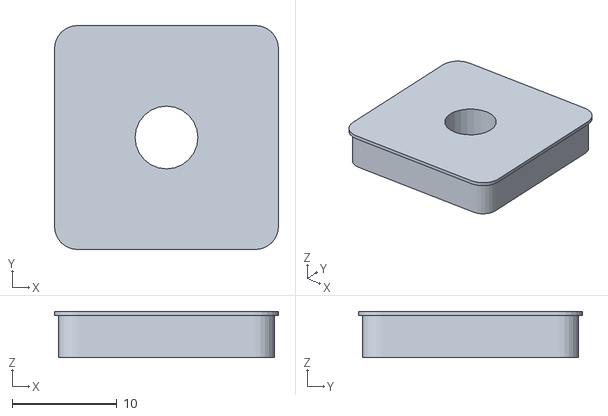
[picture p121: CAD file, 2026-04-27]
HitboardClassic/02_3D_Files/More - 更多配件 /03_其他配件/电源套件/拨杆开关底座.stl
21.4 x 21.4 x 4.40
