nopcall/hitboard/HitboardAir/02_3D_Files/180x180 打印机（A1mini ）/七星版（可加 w、shift 键）/圆润/02_定位板_左半.stl

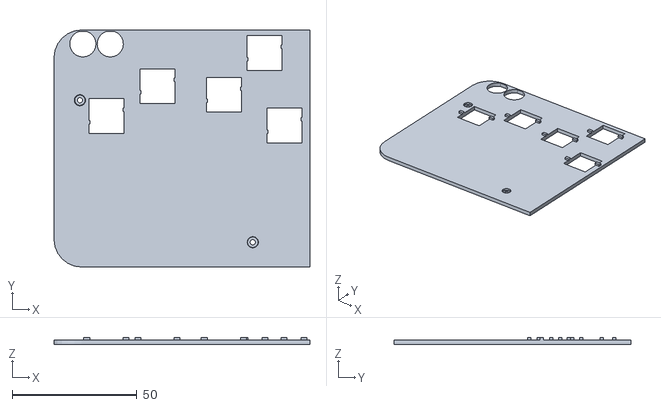
[picture p122: CAD file, 2026-04-25]
HitboardAir/02_3D_Files/180x180 打印机（A1mini ）/七星版（可加 w、shift 键）/圆润/02_定位板_左半.stl
102.8 x 95.2 x 3.00
