nopcall/hitboard/HitboardAir/02_3D_Files/180x180 打印机（A1mini ）/对称版/硬朗/03_线路板_左半.stl

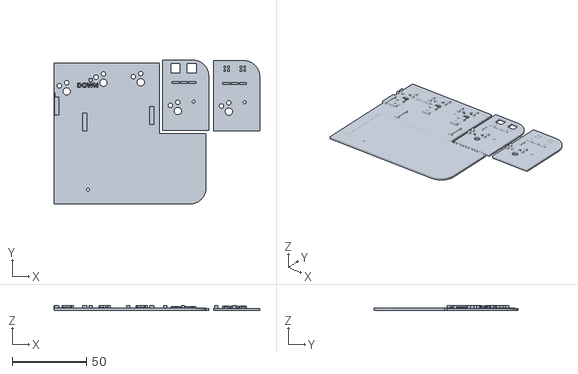
[picture p123: CAD file, 2026-04-25]
HitboardAir/02_3D_Files/180x180 打印机（A1mini ）/对称版/硬朗/03_线路板_左半.stl
139.1 x 97.5 x 3.50
