nopcall/hitboard/HitboardAir/02_3D_Files/Hitboard Air - 对称版（街霸特调）/圆润线条/01_盖板（含封帽）.stl

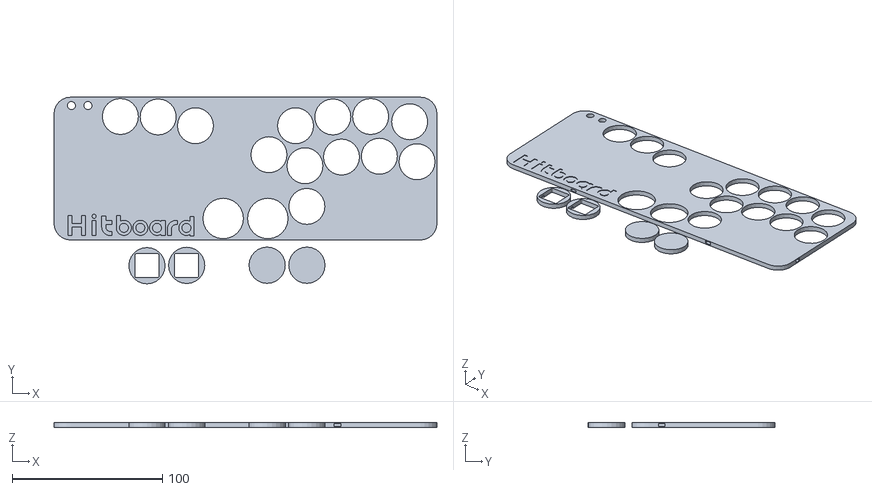
[picture p125: CAD file, 2026-04-25]
HitboardAir/02_3D_Files/Hitboard Air - 对称版（街霸特调）/圆润线条/01_盖板（含封帽）.stl
255.2 x 124.4 x 3.40
