nopcall/hitboard/HitboardAir/02_3D_Files/More - 更多配件 /00_按键配件/配件_功能键/全能套装.stl

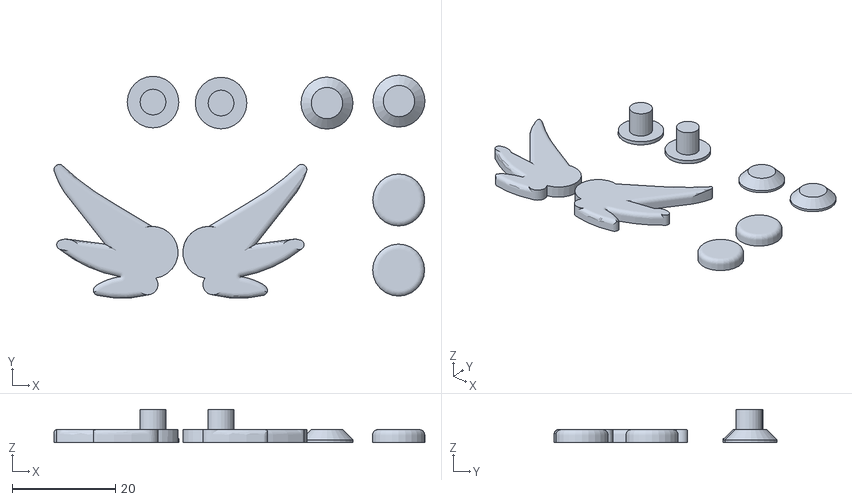
[picture p126: CAD file, 2026-04-25]
HitboardAir/02_3D_Files/More - 更多配件 /00_按键配件/配件_功能键/全能套装.stl
71.8 x 43.2 x 6.40
