nopcall/hitboard/HitboardAir/02_3D_Files/More - 更多配件 /02_盖板配件/23mm摇杆封帽.stl

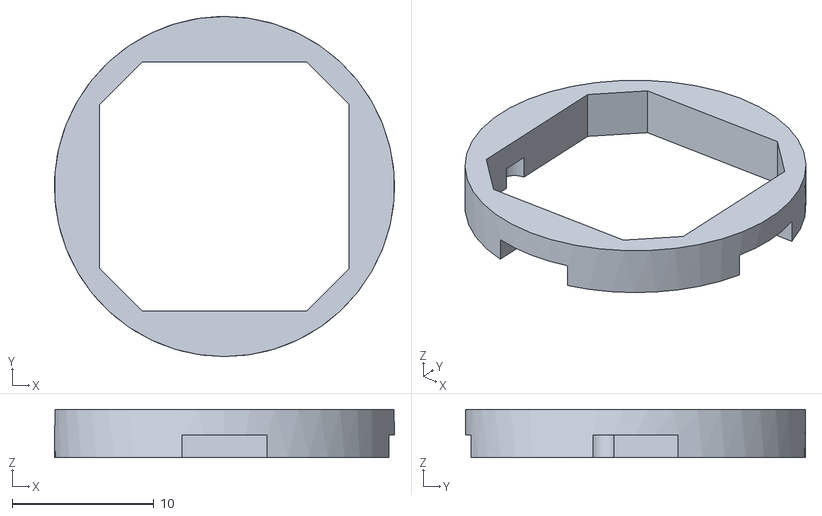
[picture p127: CAD file, 2026-04-25]
HitboardAir/02_3D_Files/More - 更多配件 /02_盖板配件/23mm摇杆封帽.stl
24.0 x 24.0 x 3.40
