nopcall/hitboard/HitboardClassic/02_3D_Files/Hitboard Classic - 大杯 L/新大杯 （L）/外壳组件（含锁扣）.stl

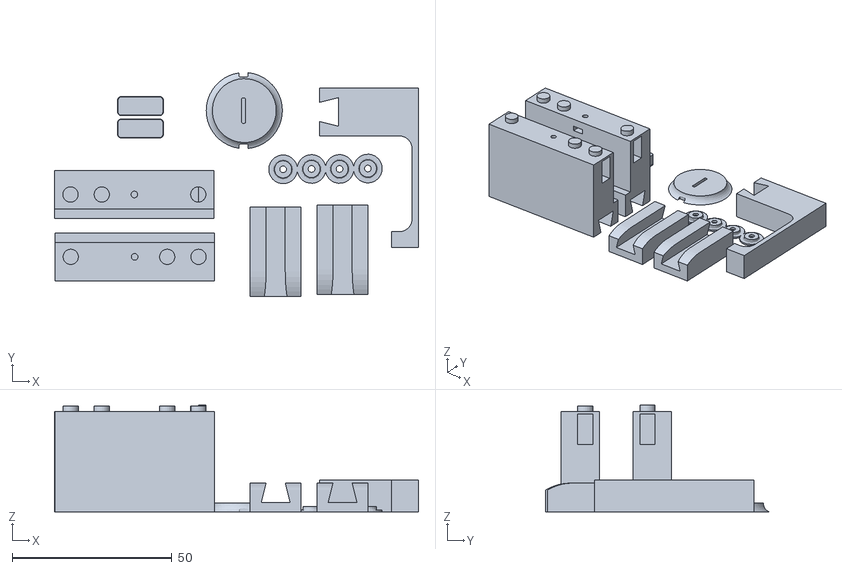
[picture p128: CAD file, 2026-05-03]
HitboardClassic/02_3D_Files/Hitboard Classic - 大杯 L/新大杯 （L）/外壳组件（含锁扣）.stl
113.9 x 70.0 x 33.4
