nopcall/hitboard/HitboardClassic/02_3D_Files/More - 更多配件 /00_按键/00_键帽/键帽-Mixboard 宽按键.stl

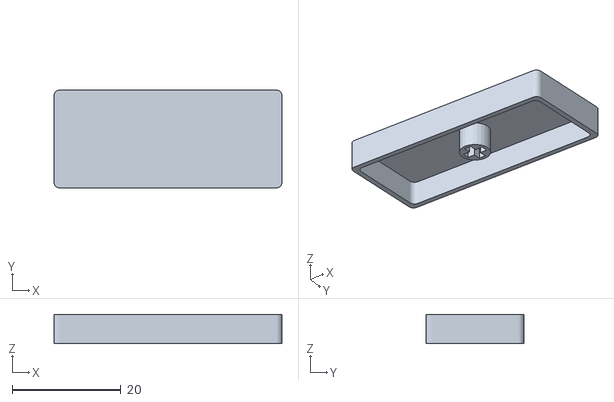
[picture p129: CAD file, 2026-04-22]
HitboardClassic/02_3D_Files/More - 更多配件 /00_按键/00_键帽/键帽-Mixboard 宽按键.stl
42.0 x 18.0 x 5.40
