nopcall/hitboard/HitboardClassic/02_3D_Files/More - 更多配件 /02_外壳配件/轨道-束线器.stl

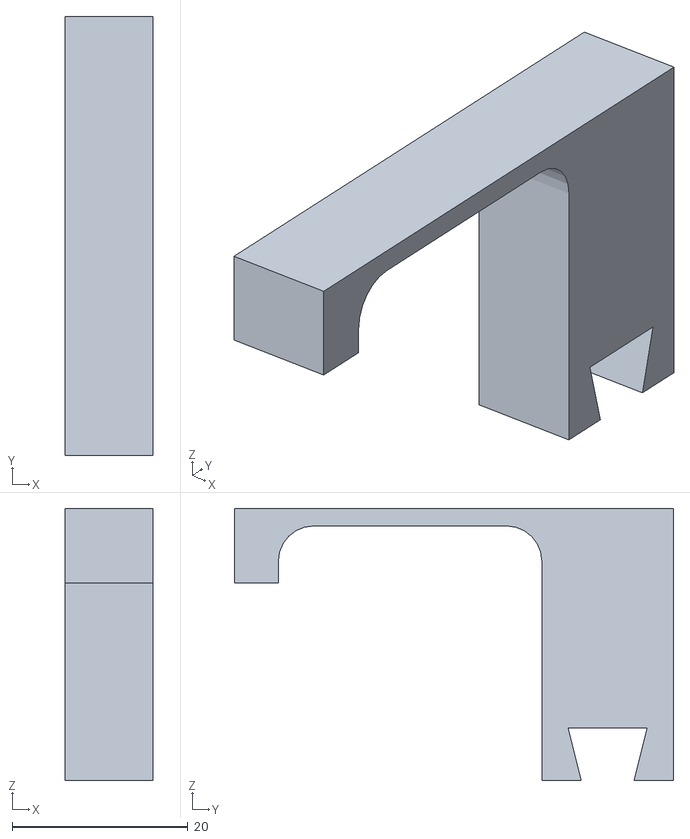
[picture p131: CAD file, 2026-04-22]
HitboardClassic/02_3D_Files/More - 更多配件 /02_外壳配件/轨道-束线器.stl
10.00 x 50.0 x 31.0
