nopcall/hitboard/HitboardClassic/02_3D_Files/More - 更多配件 /03_其他配件/电源套件/拨杆开关底座-挡片.stl

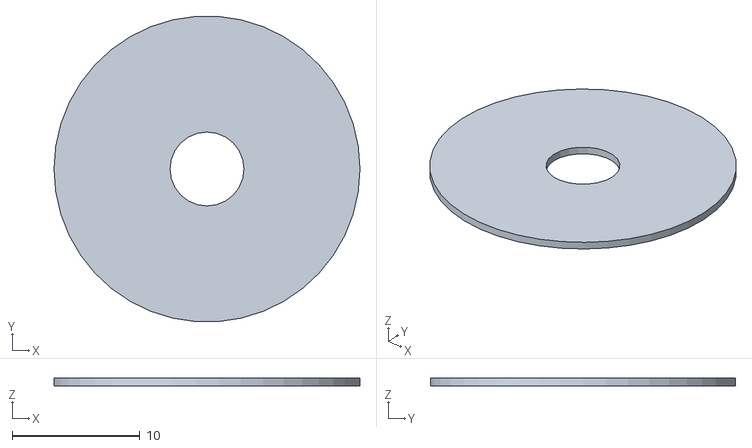
[picture p132: CAD file, 2026-04-22]
HitboardClassic/02_3D_Files/More - 更多配件 /03_其他配件/电源套件/拨杆开关底座-挡片.stl
24.0 x 23.9 x 0.6
