nopcall/hitboard/HitboardClassic/02_3D_Files/More - 更多配件 /内测入口/用于23mm 键帽（会不兼容 24mm 街机按键）/键帽圆润.stl

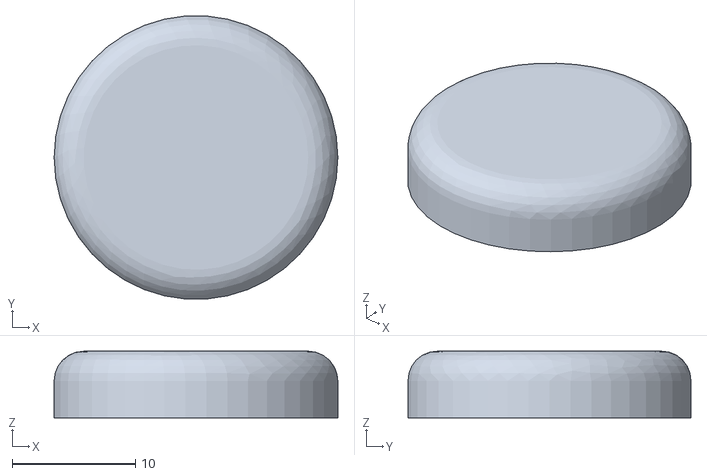
[picture p133: CAD file, 2026-05-09]
HitboardClassic/02_3D_Files/More - 更多配件 /内测入口/用于23mm 键帽（会不兼容 24mm 街机按键）/键帽圆润.stl
23.0 x 22.9 x 5.40
