nopcall/hitboard/HitboardClassic/02_3D_Files/More - 更多配件 /00_按键/00_键帽/键帽-拨片.stl

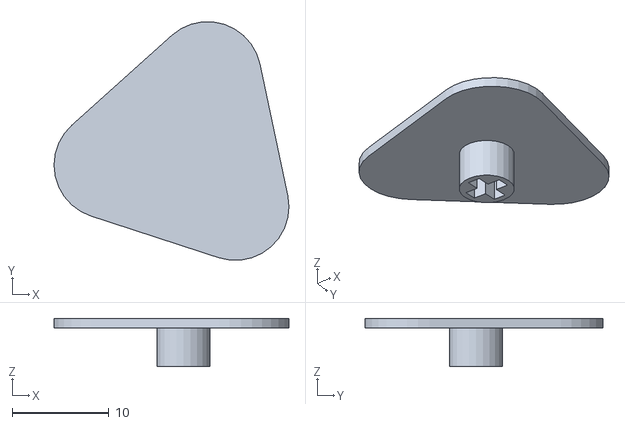
[picture p135: CAD file, 2026-04-22]
HitboardClassic/02_3D_Files/More - 更多配件 /00_按键/00_键帽/键帽-拨片.stl
24.3 x 24.6 x 5.00
